watterott/SilentStepStick/hardware/SilentStepStick-TMC2208_v13.jpg

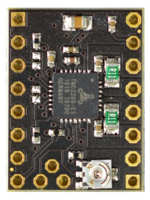
hardware/SilentStepStick-TMC2208_v13.jpg
