watterott/SilentStepStick/hardware/SilentStepStick-TMC2209_v20.jpg

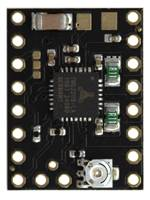
hardware/SilentStepStick-TMC2209_v20.jpg
