watterott/SilentStepStick/hardware/SilentStepStick-TMC5160_v14.pdf

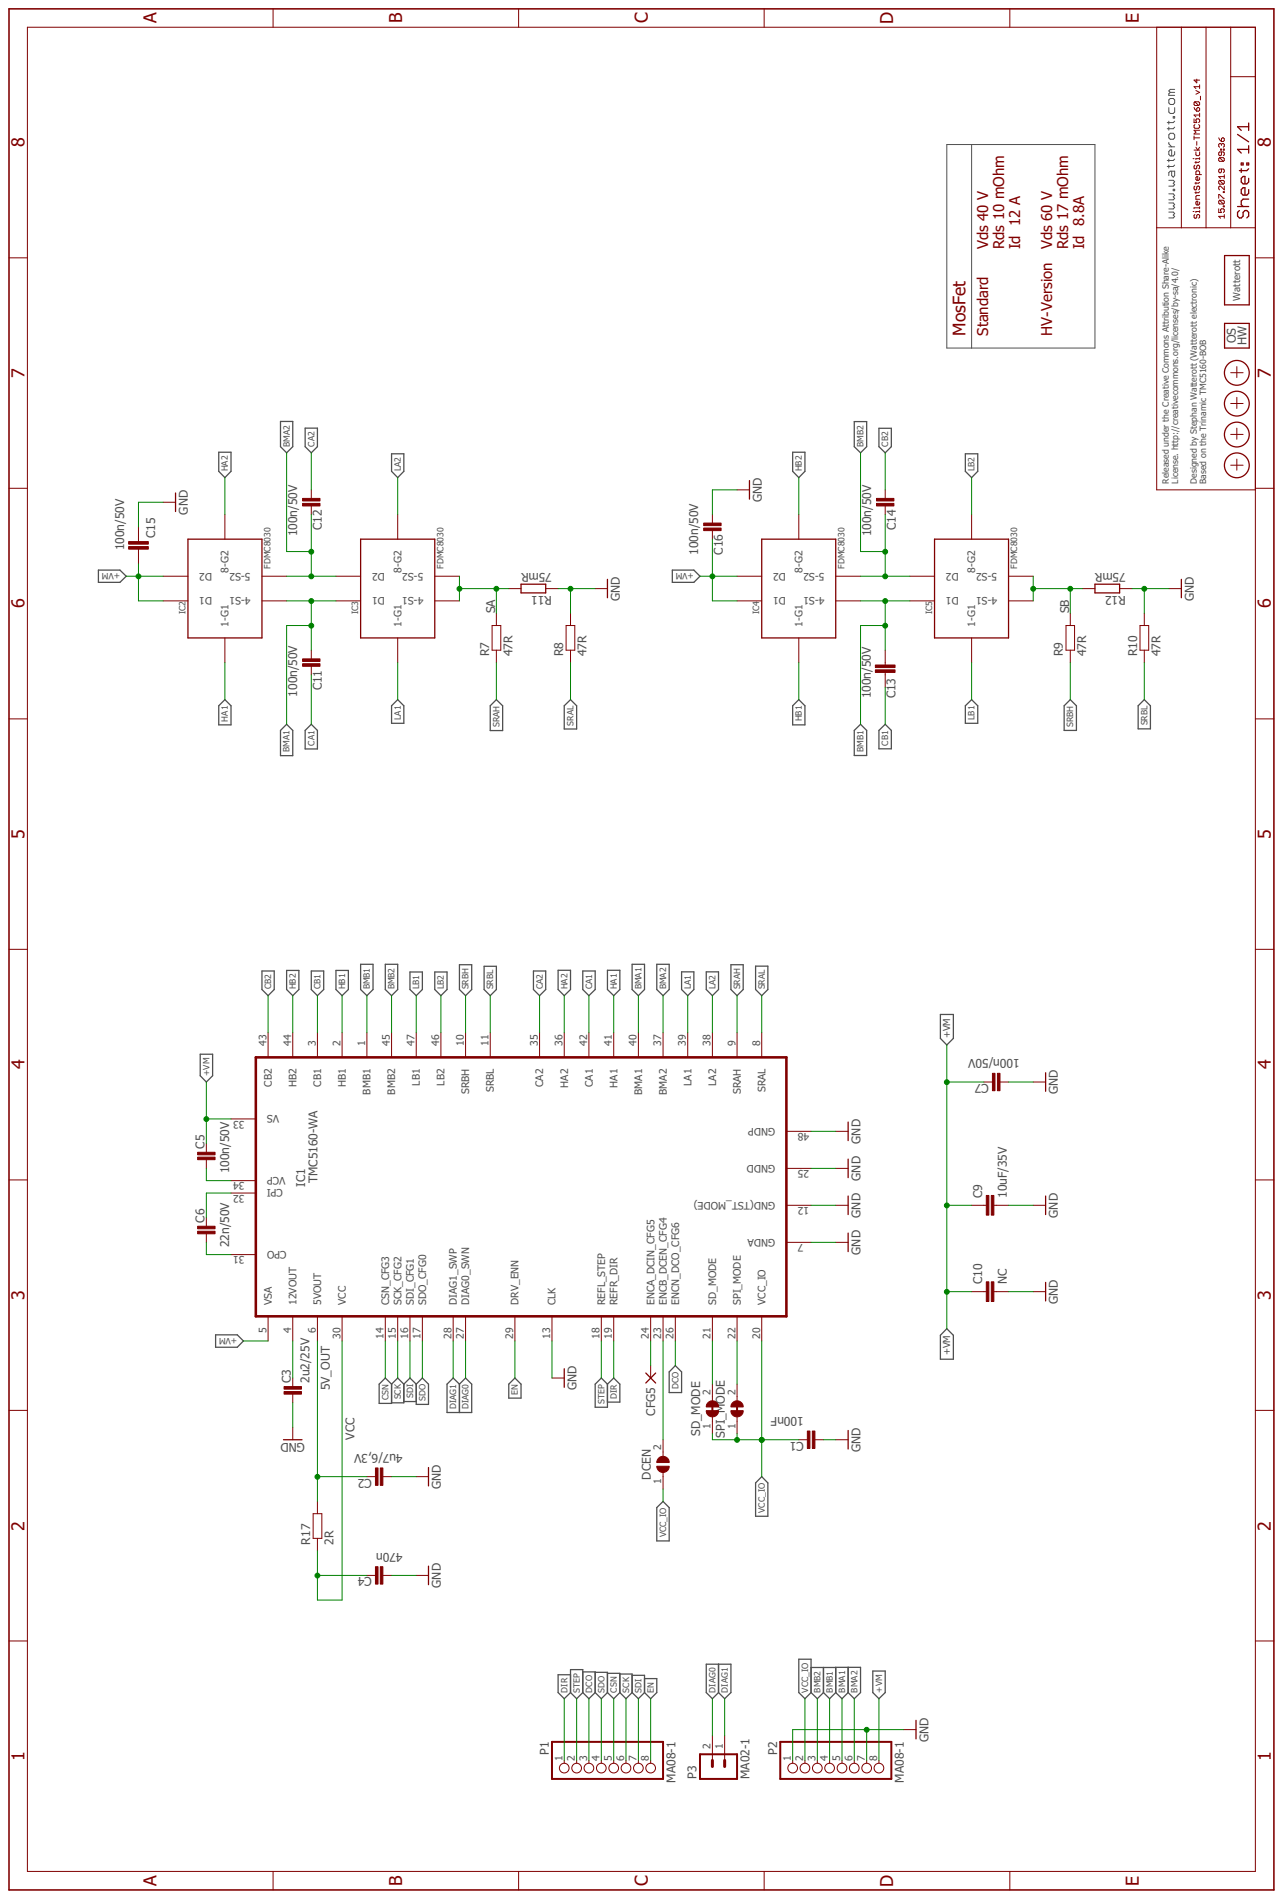
[picture p28: page 1]

MosFet Standard HV-Version

Released under the Creative Commons Attribution Share-Alike

License. http://creativecommons.org/licenses/by-sa/4.0/ Designed by Stephan Watterott (Watterott electronic) Based on the Trinamic TMC5160-BOB

10uF/35V NC GND GND GND

GND GND

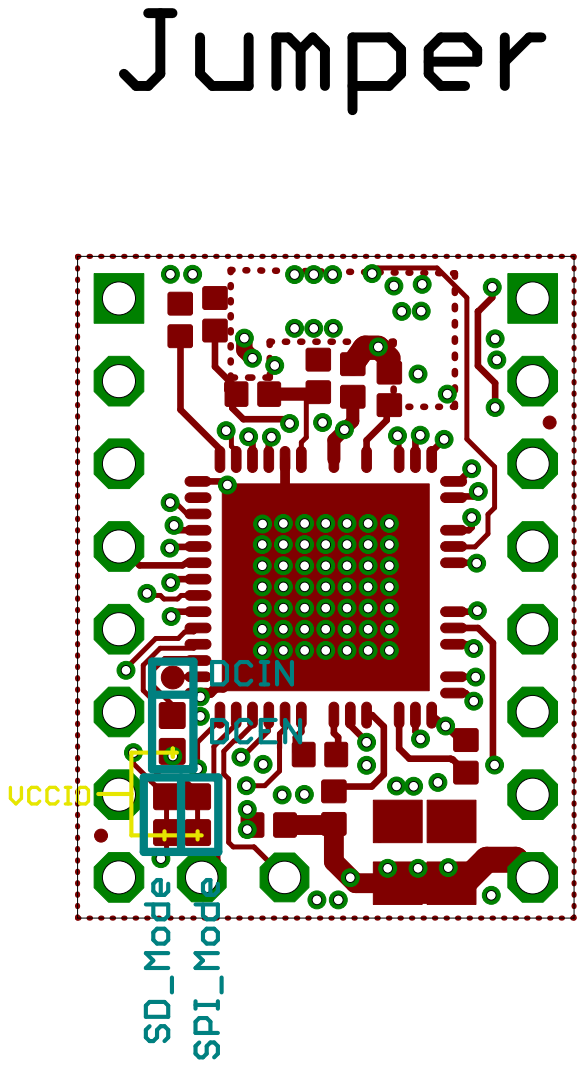
[picture p29: page 2]

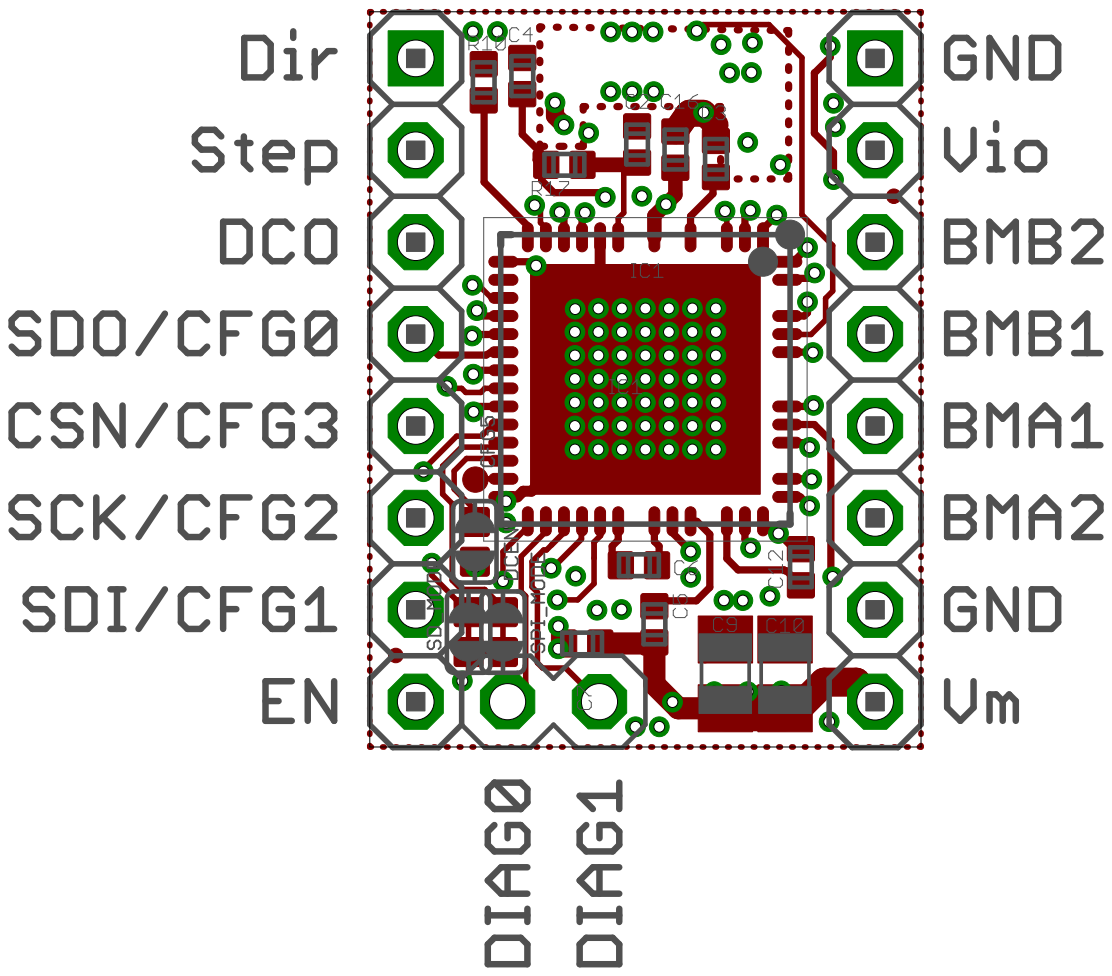
[picture p30: page 3]

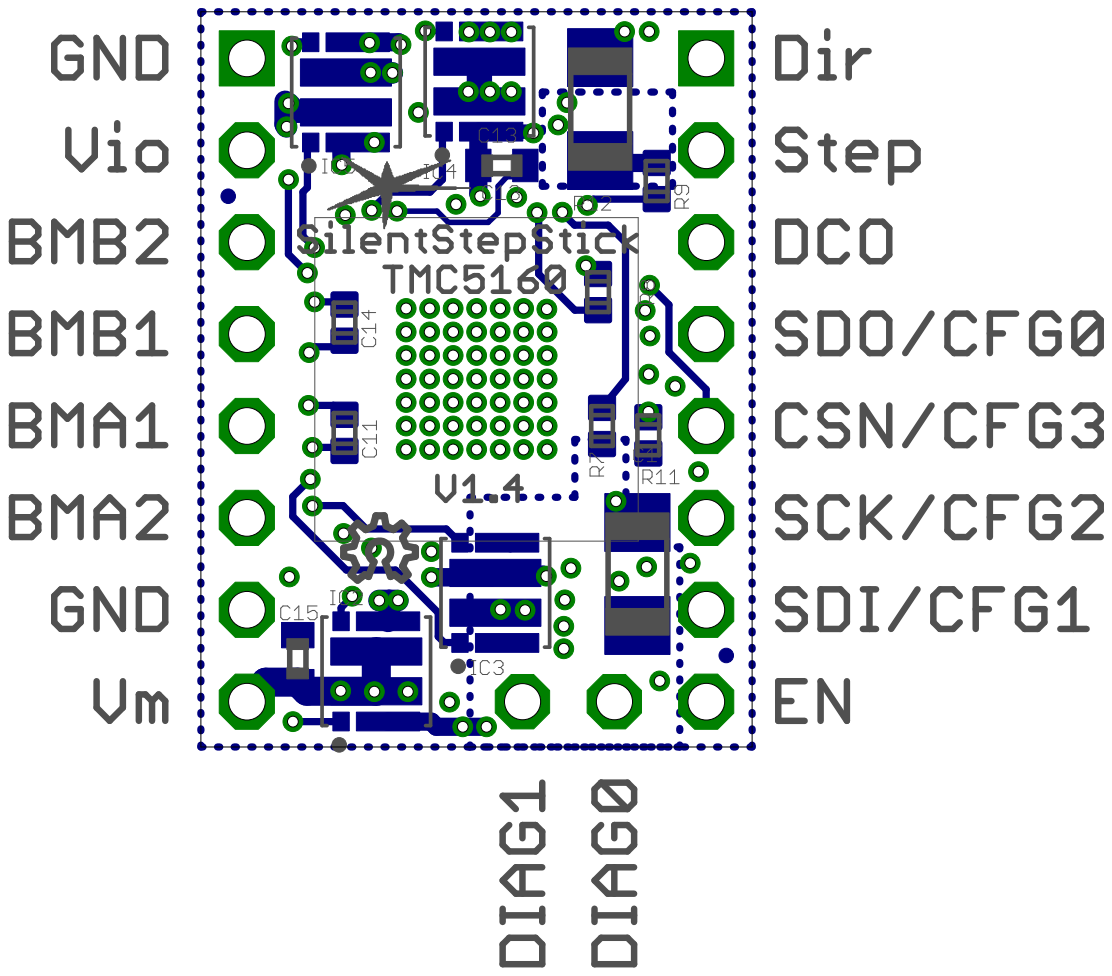
[picture p31: page 4]
