watterott/SilentStepStick/hardware/SilentStepStick-TMC5160_v13.pdf

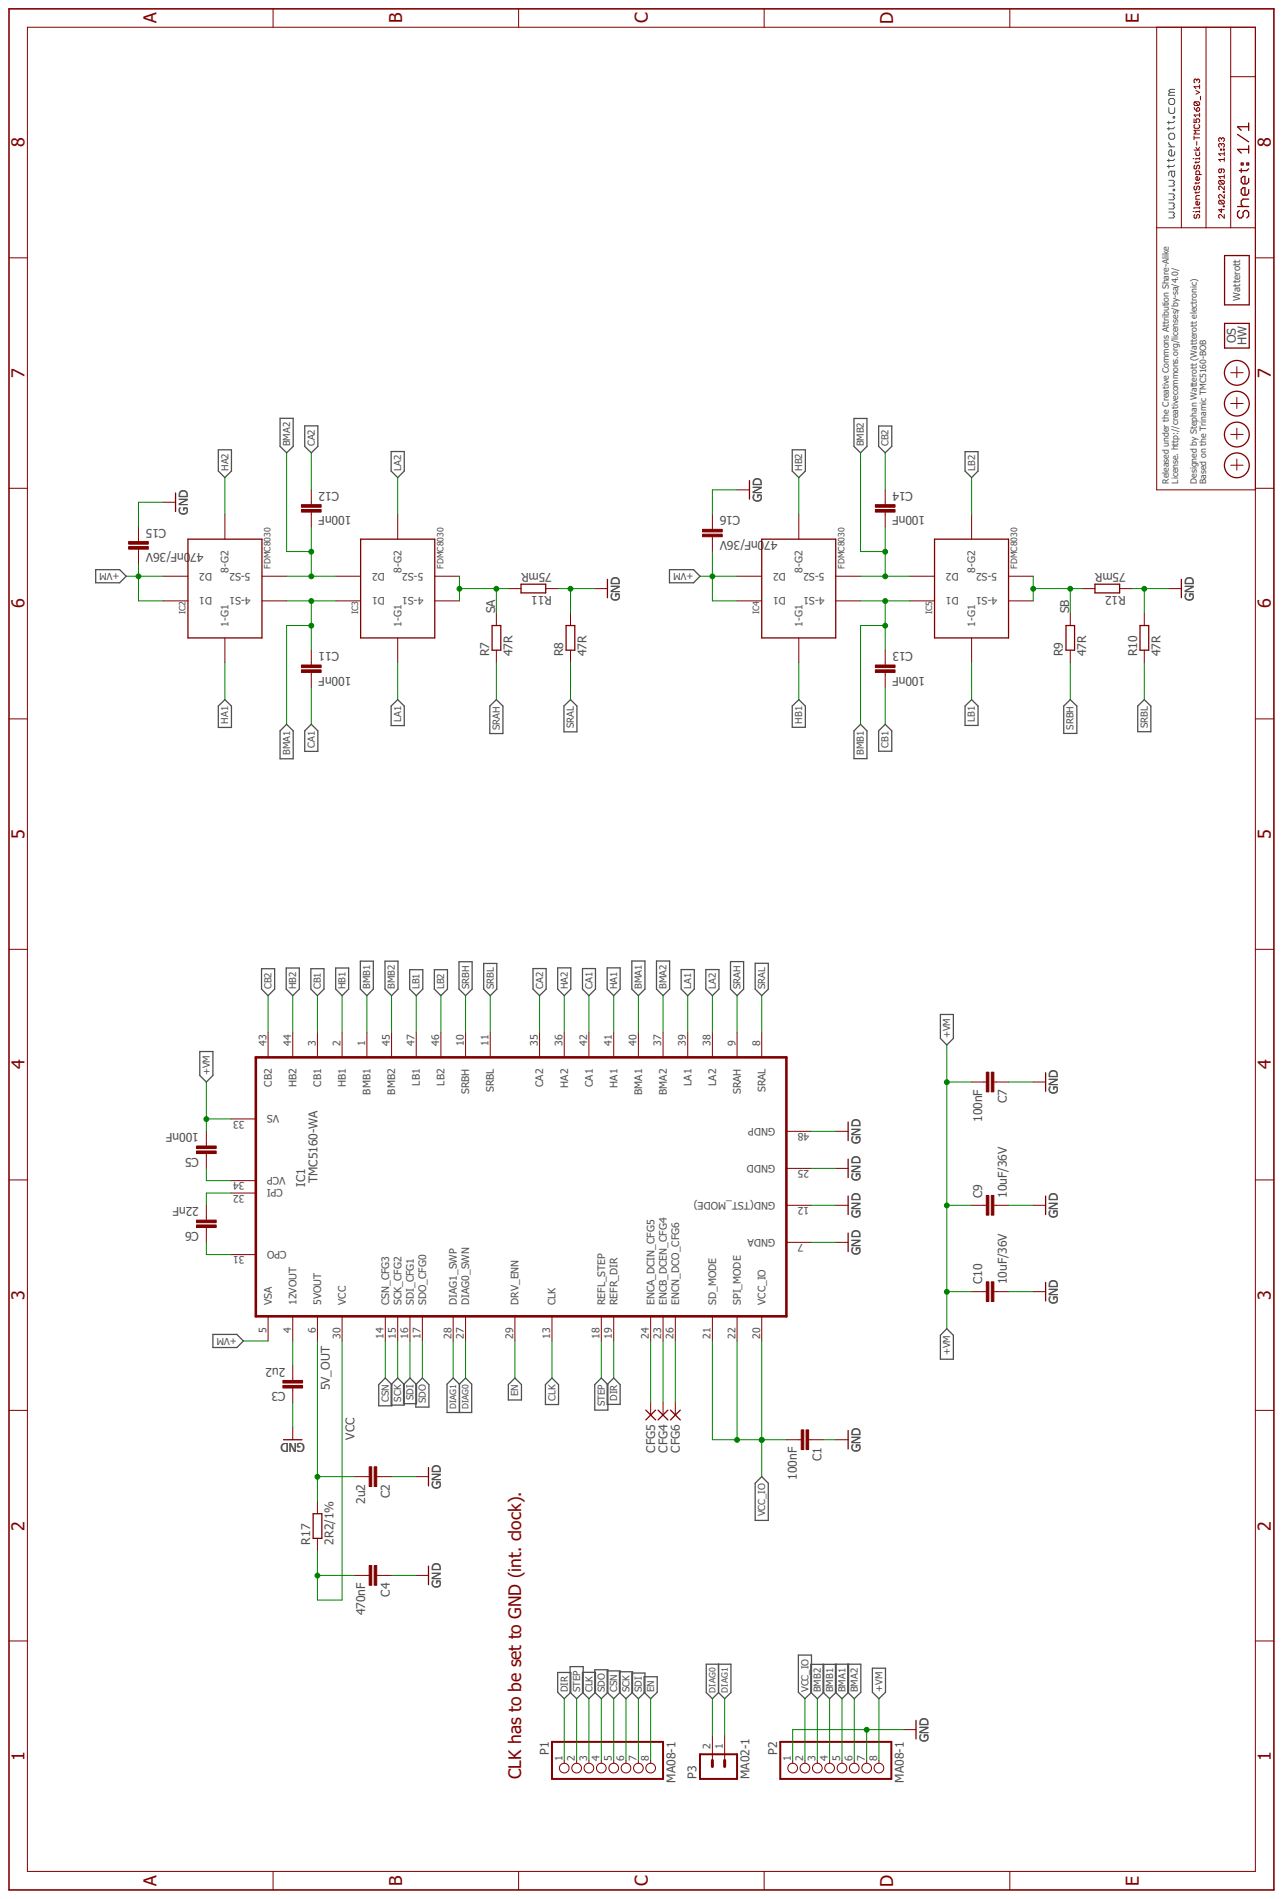
[picture p32: page 1]

Released under the Creative Commons Attribution Share-Alike

License. http://creativecommons.org/licenses/by-sa/4.0/ Designed by Stephan Watterott (Watterott electronic) Based on the Trinamic TMC5160-BOB

GND GND

STEP STEP DIR DIR

CLK has to be set to GND (int. clock).

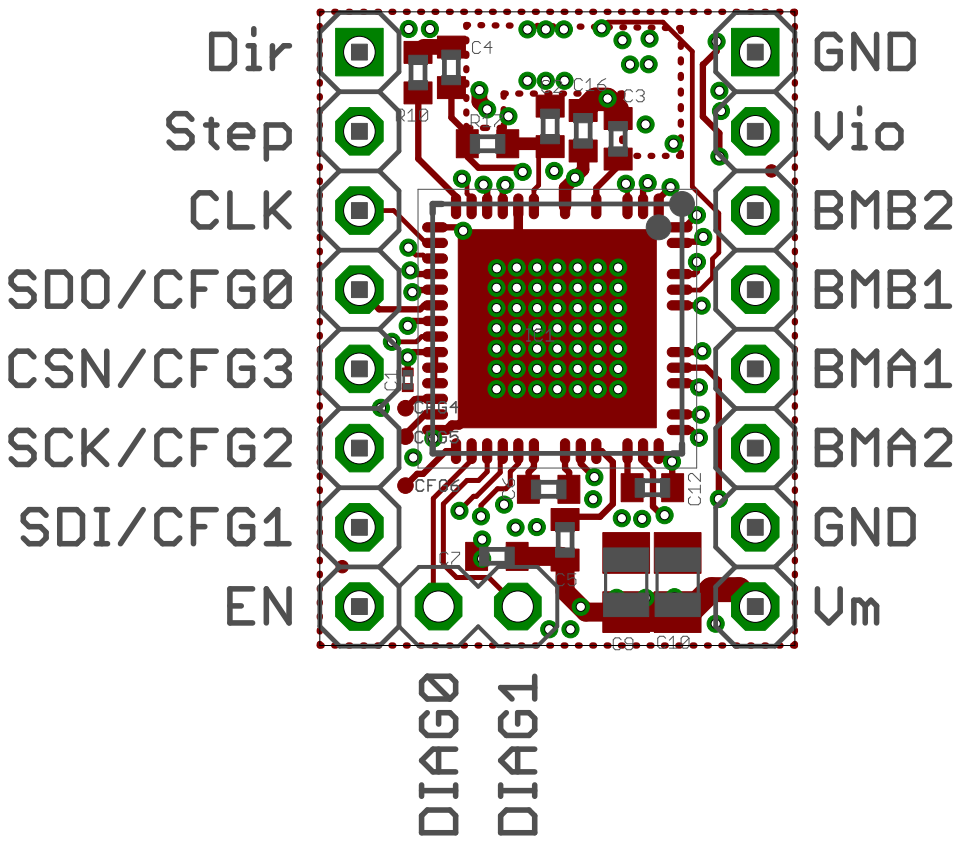
[picture p33: page 2]

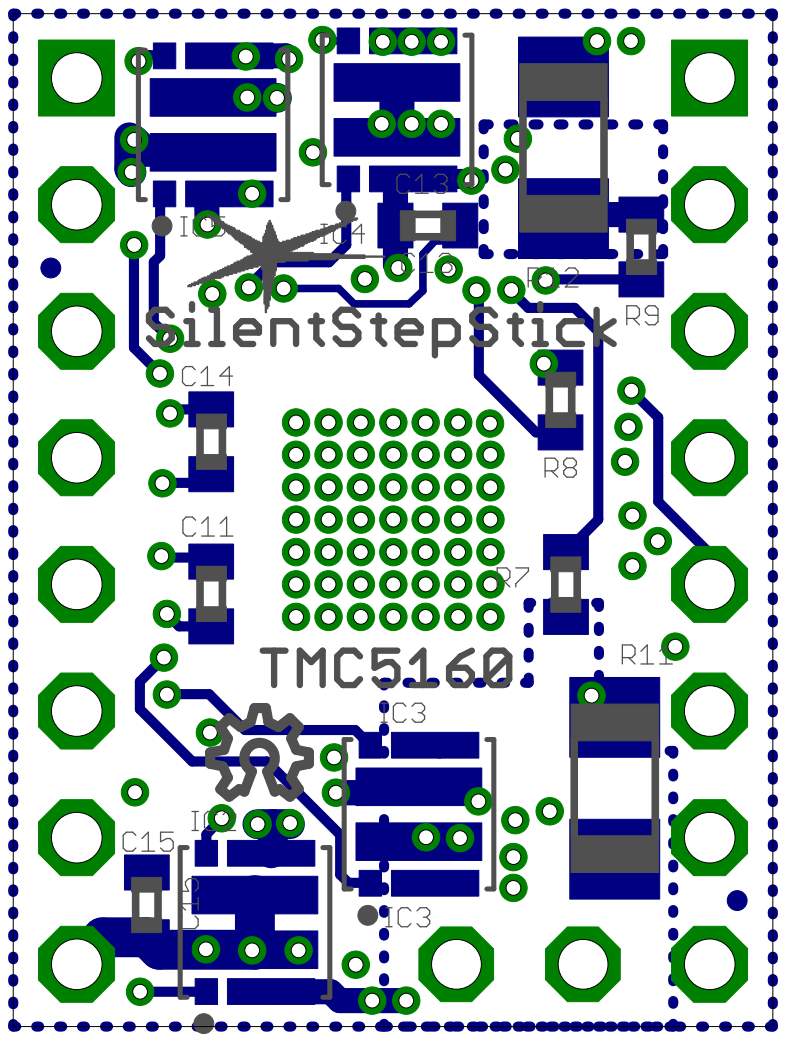
[picture p34: page 3]
