watterott/SilentStepStick/hardware/SilentStepStick-TMC2100_v13_5V.pdf

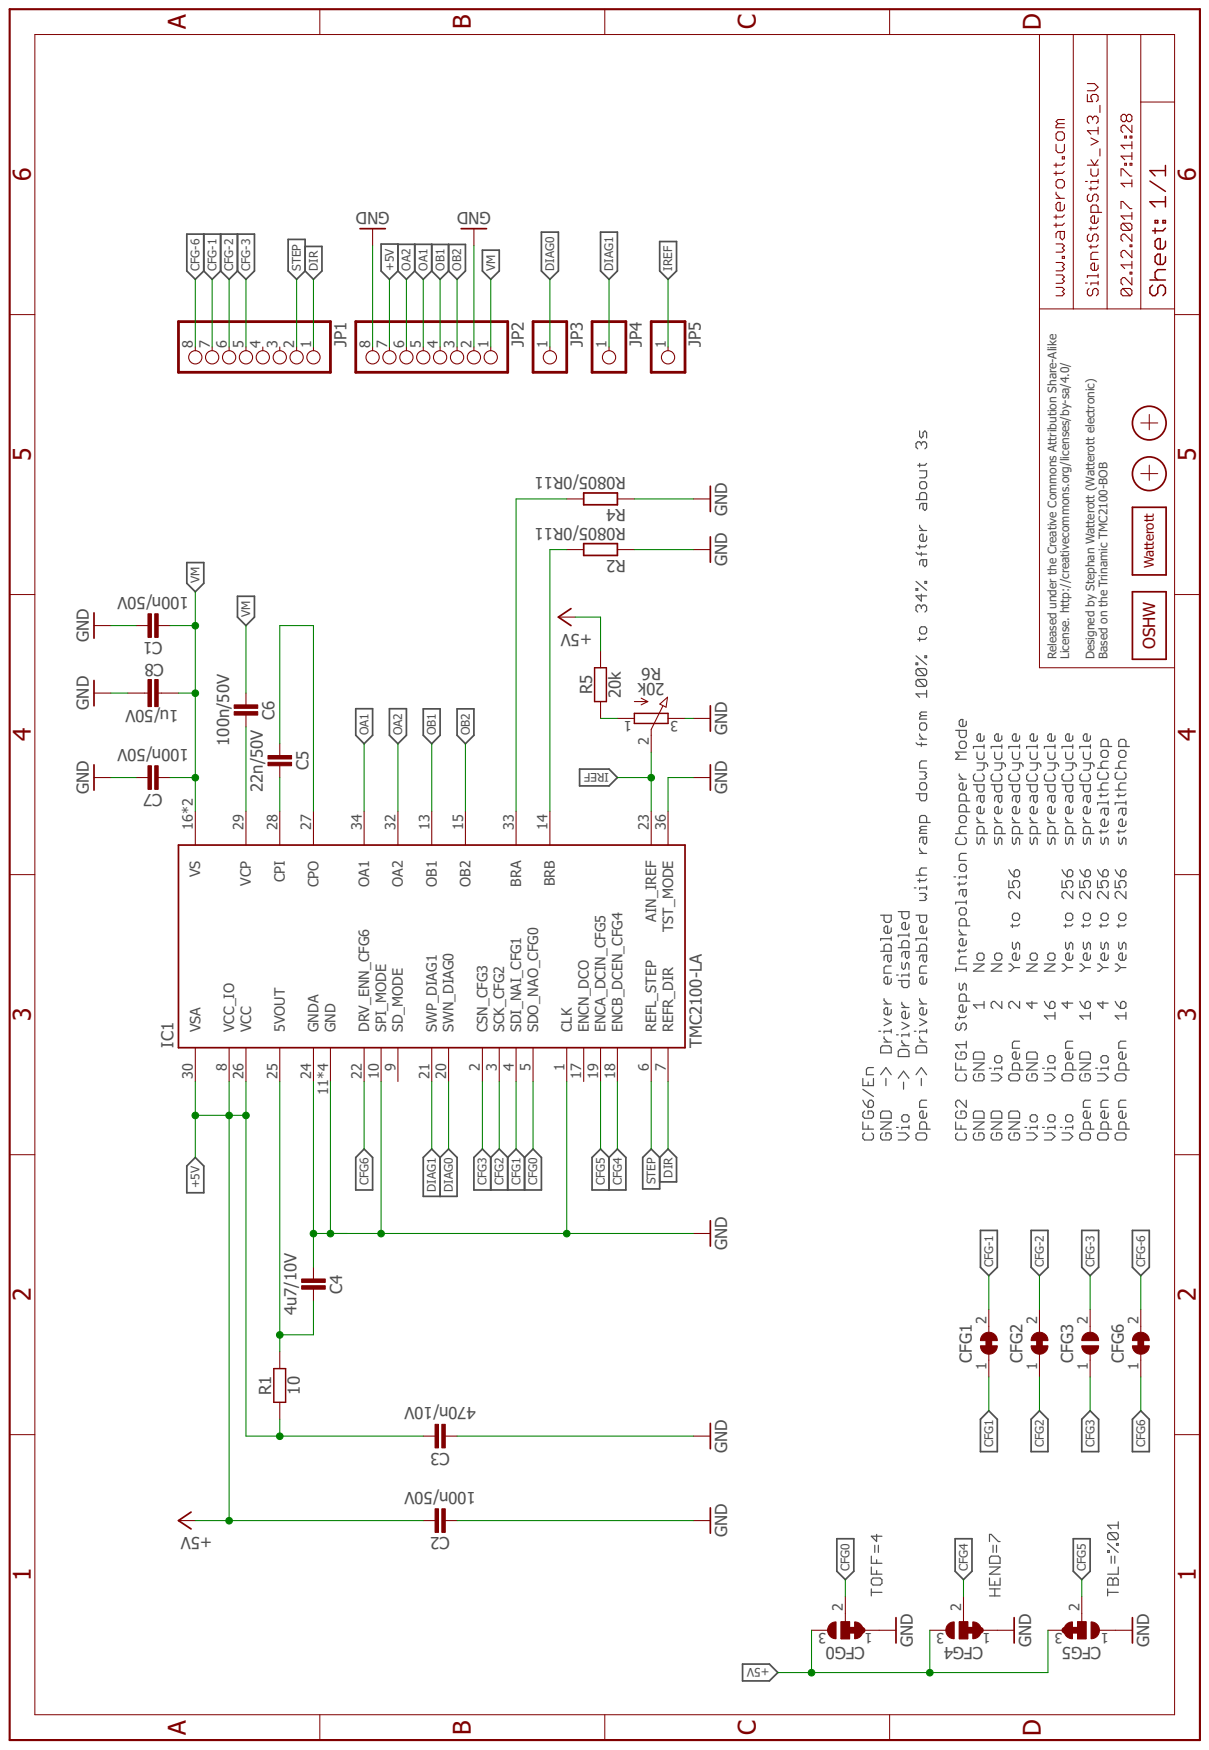
[picture p35: page 1]

Released under the Creative Commons At ribution Share-Alike

License. http://creativecommons.org/licenses/by-sa/4.0/ Designed by Stephan Watterott (Watterott electronic) Based on the Trinamic TMC2100-BOB

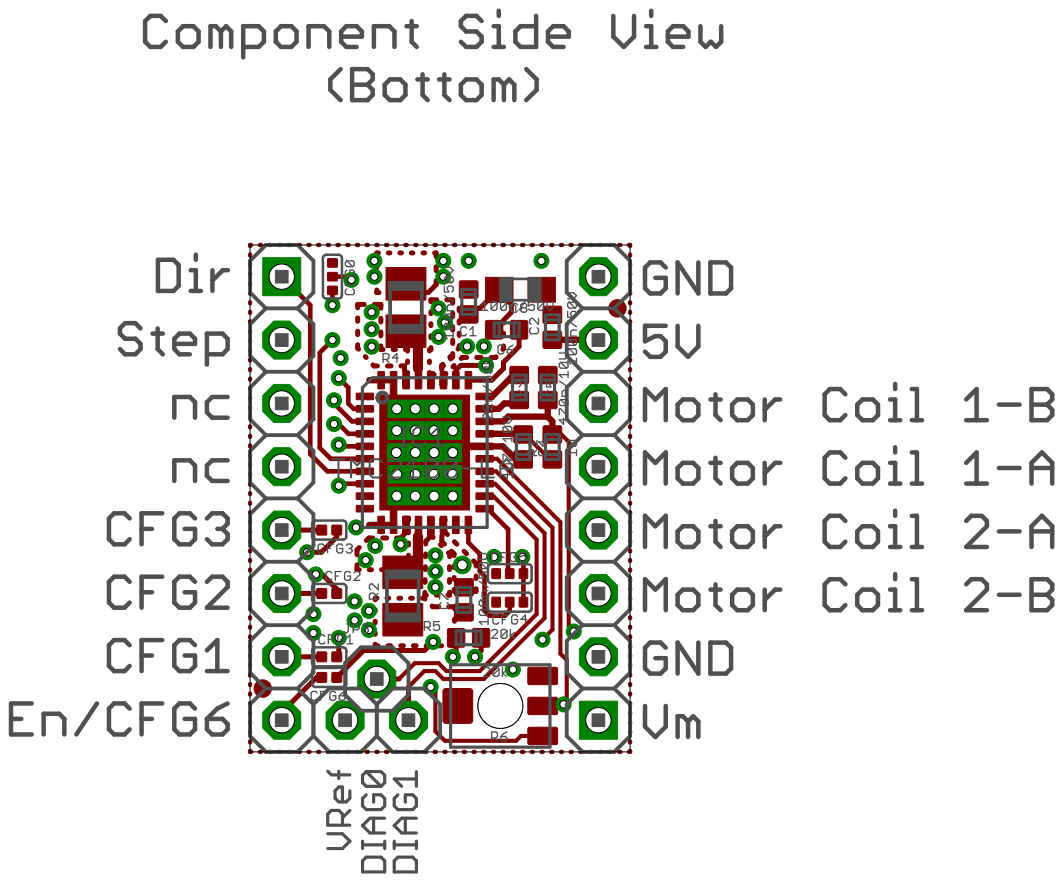
[picture p36: page 2]

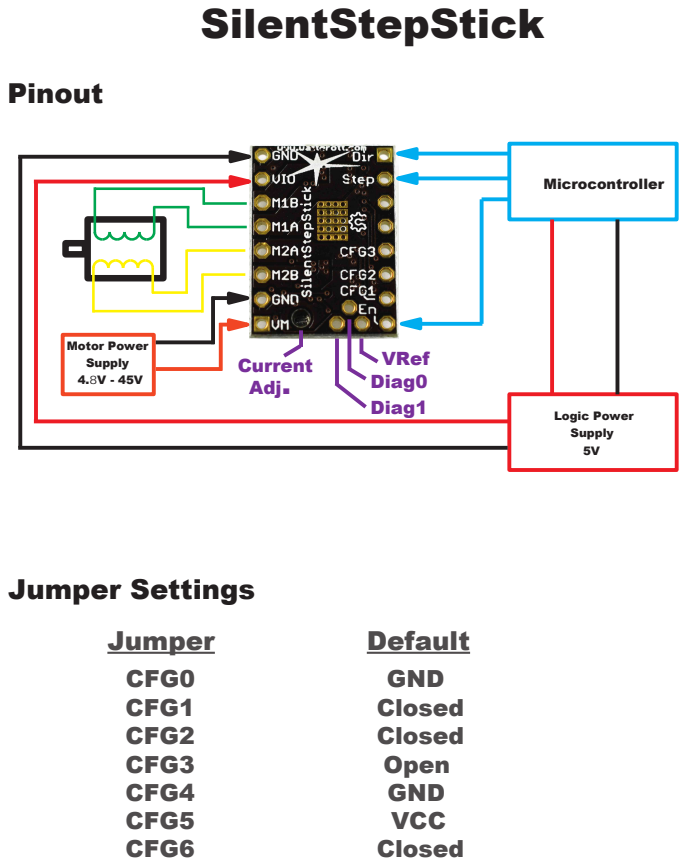
[picture p37: page 3]

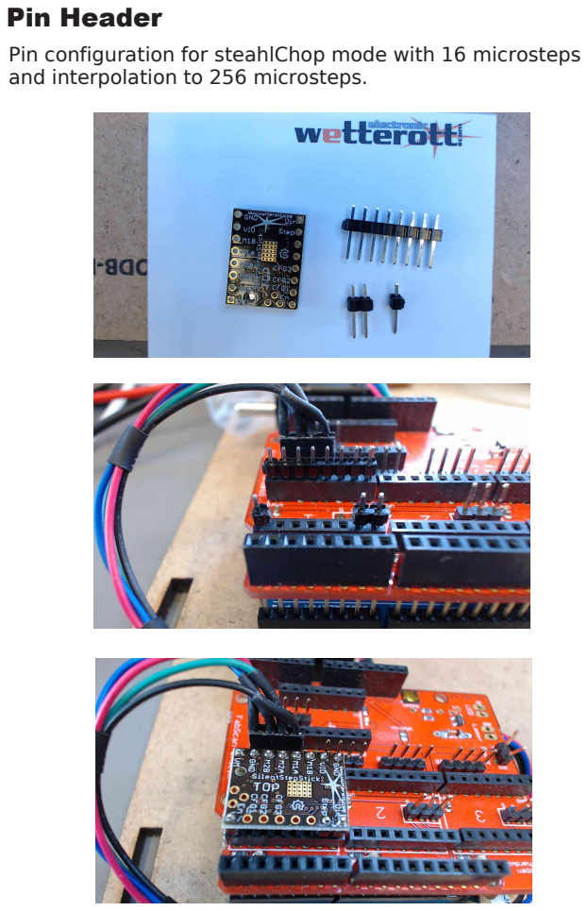
[picture p38: page 4]

Pin configuration for steahlChop mode with 16 microsteps
and interpolation to 256 microsteps.
