watterott/SilentStepStick/hardware/SilentStepStick-TMC2100_v13.pdf

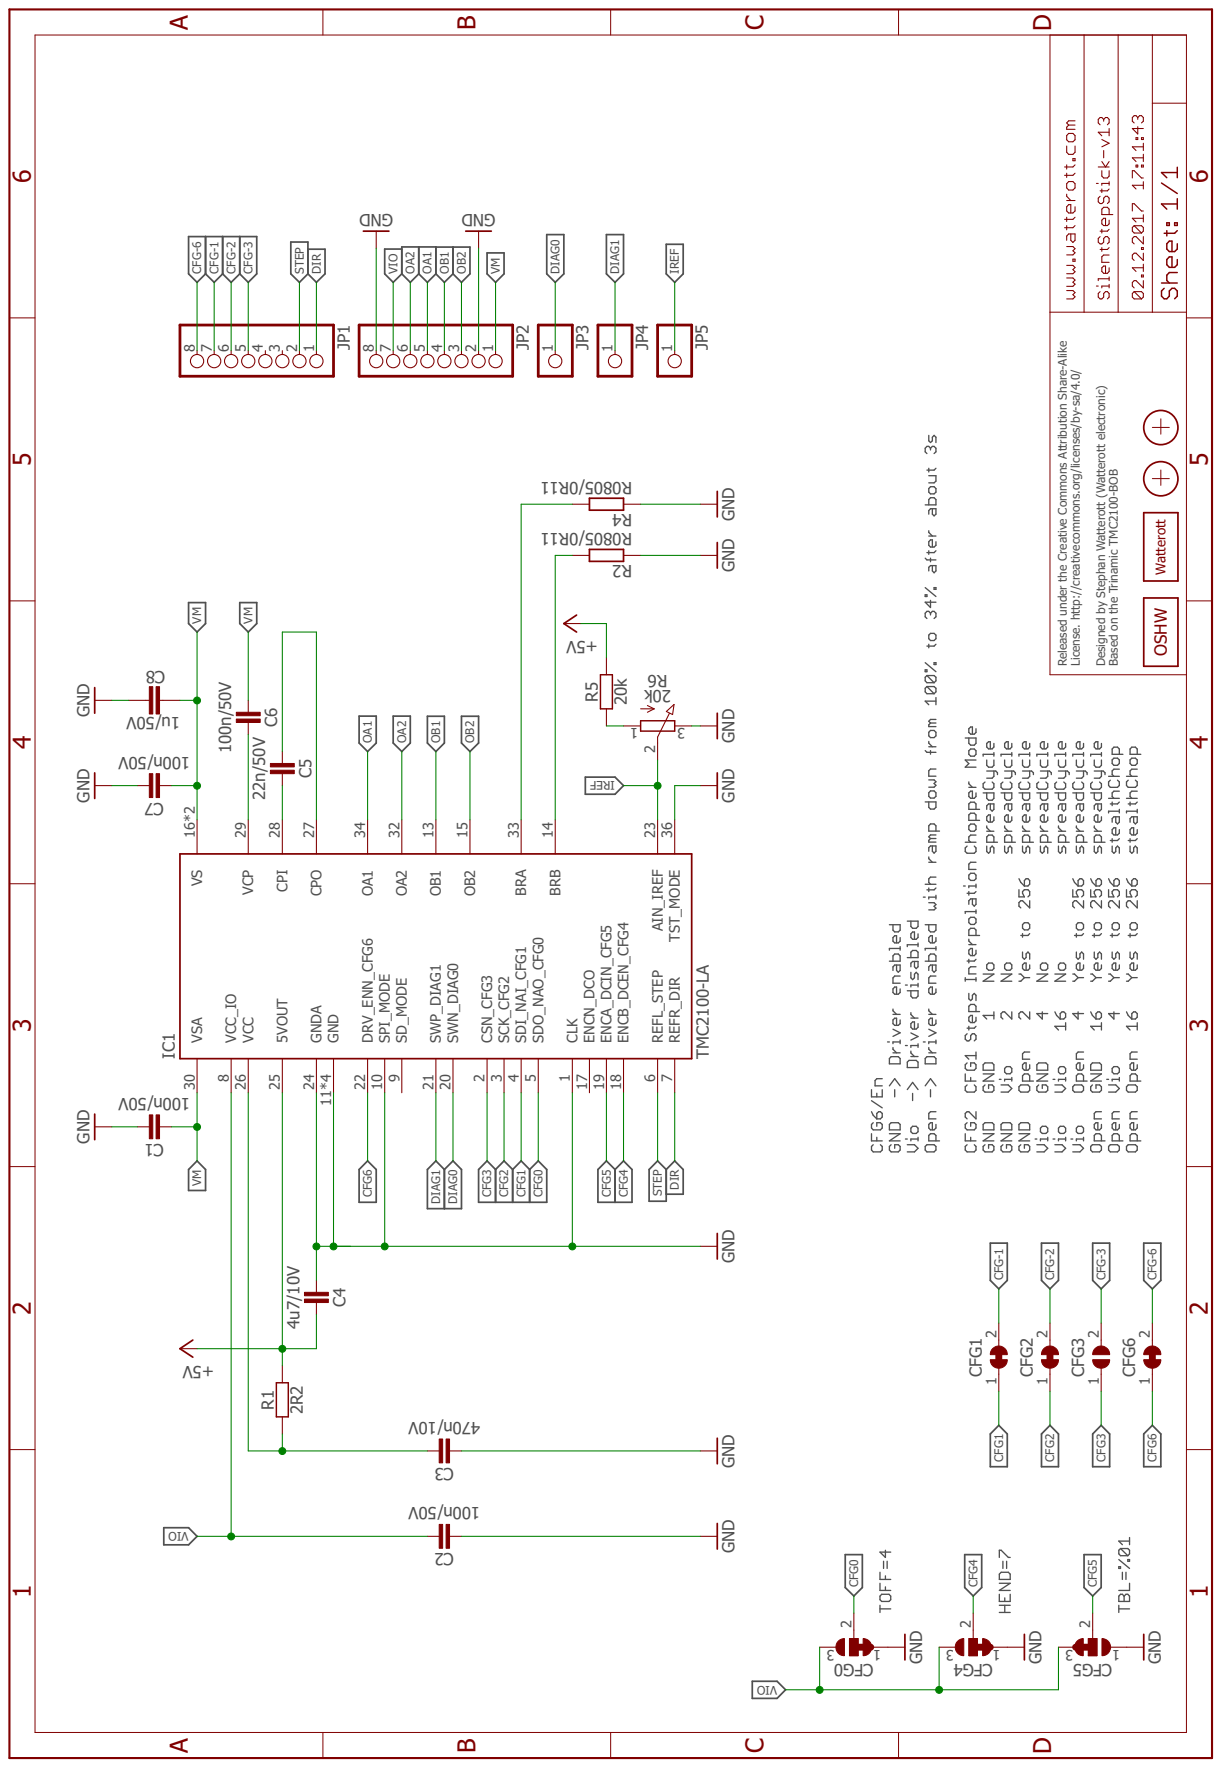
[picture p39: page 1]

Released under the Creative Commons At ribution Share-Alike

License. http://creativecommons.org/licenses/by-sa/4.0/ Designed by Stephan Watterott (Watterott electronic) Based on the Trinamic TMC2100-BOB

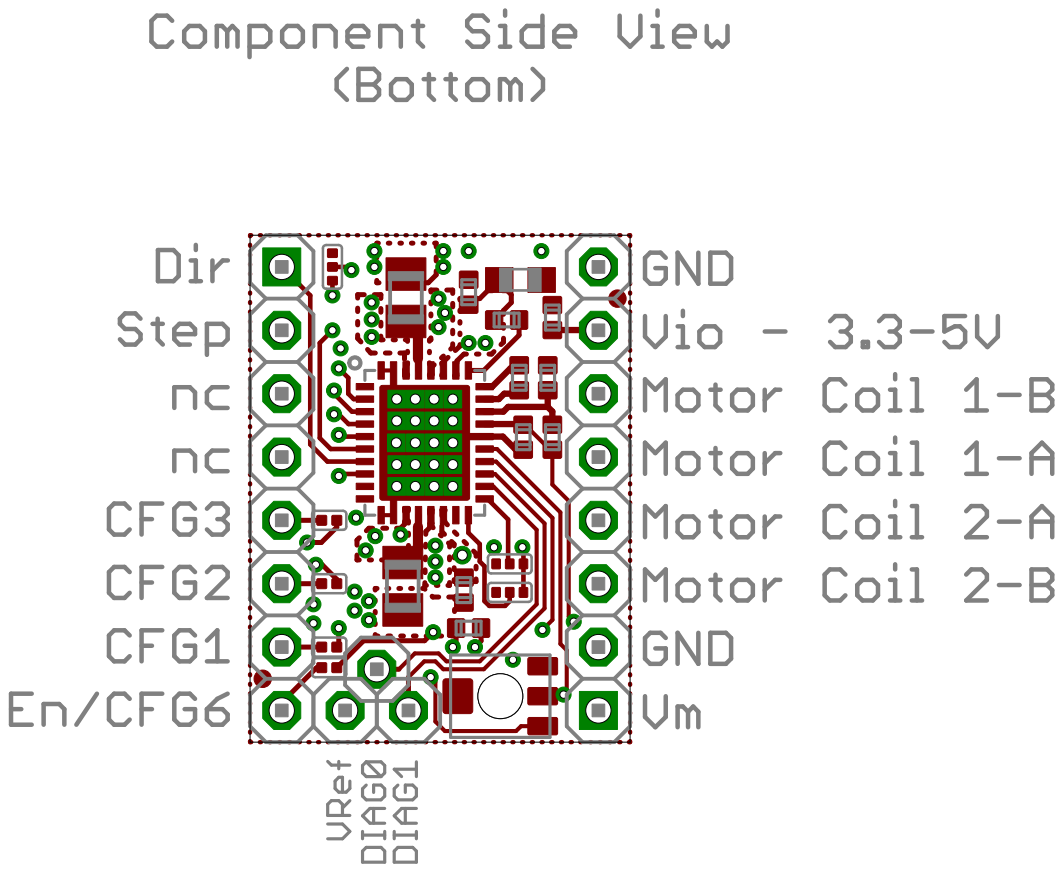
[picture p40: page 2]

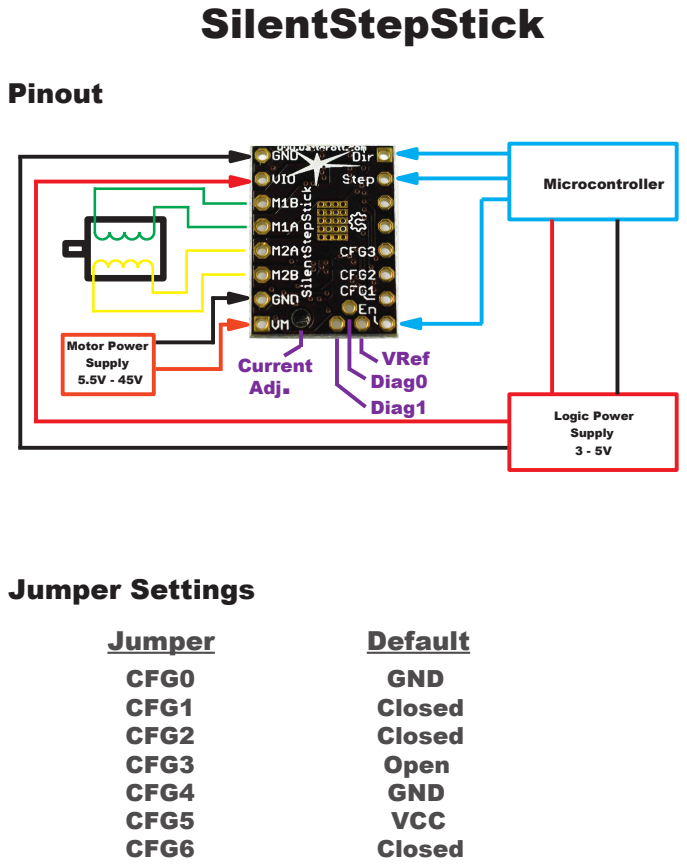
[picture p41: page 3]


Pin configuration for steahlChop mode with 16 microsteps
and interpolation to 256 microsteps.
