watterott/SilentStepStick/hardware/SilentStepStick-TMC2100_v11.pdf

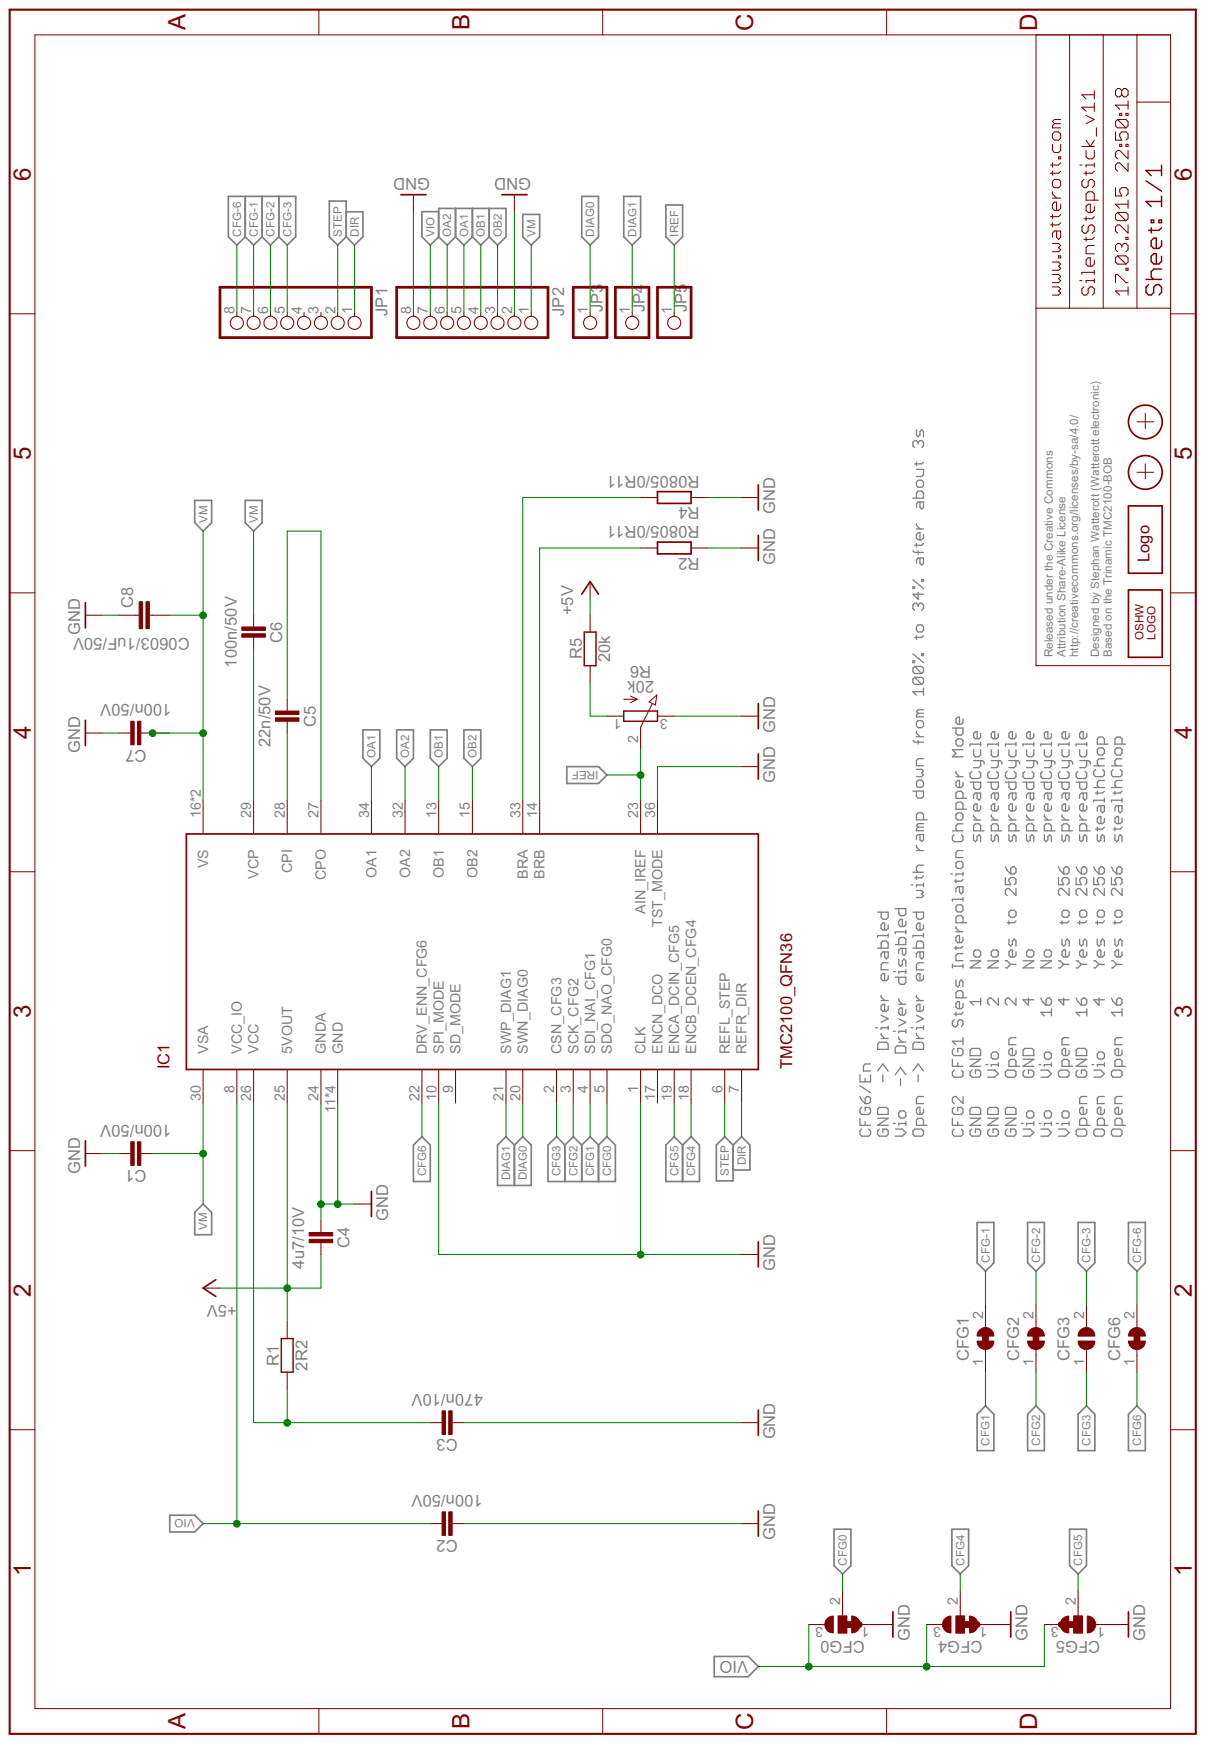
[picture p42: page 1]

Designed by Stephan Watterott (Watterott electronic)

http://creativecommons.org/licenses/by-sa/4.0/

Released under the Creative Commons

Based on the Trinamic TMC2100-BOB

GND GND

Attribution Share-Alike License

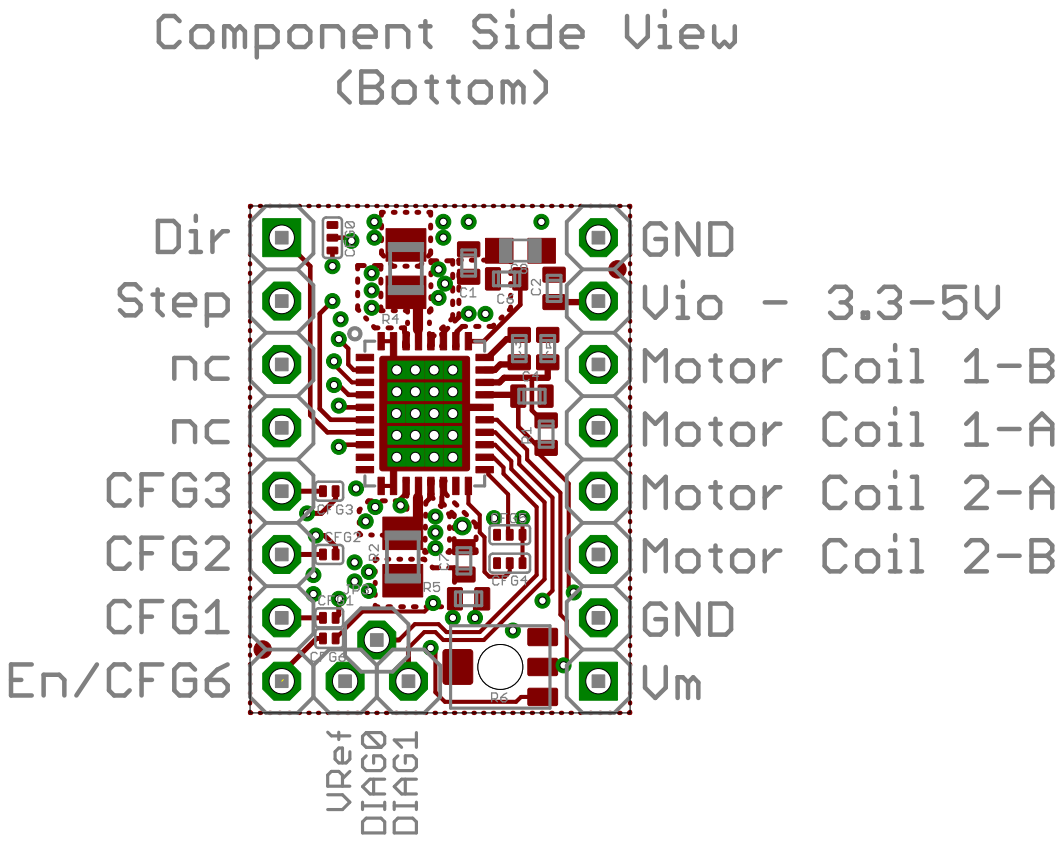
[picture p43: page 2]



Pin configuration for steahlChop mode with 16 microsteps
and interpolation to 256 microsteps.
