watterott/SilentStepStick/hardware/SilentStepStick-TMC2100_v12_5V.pdf

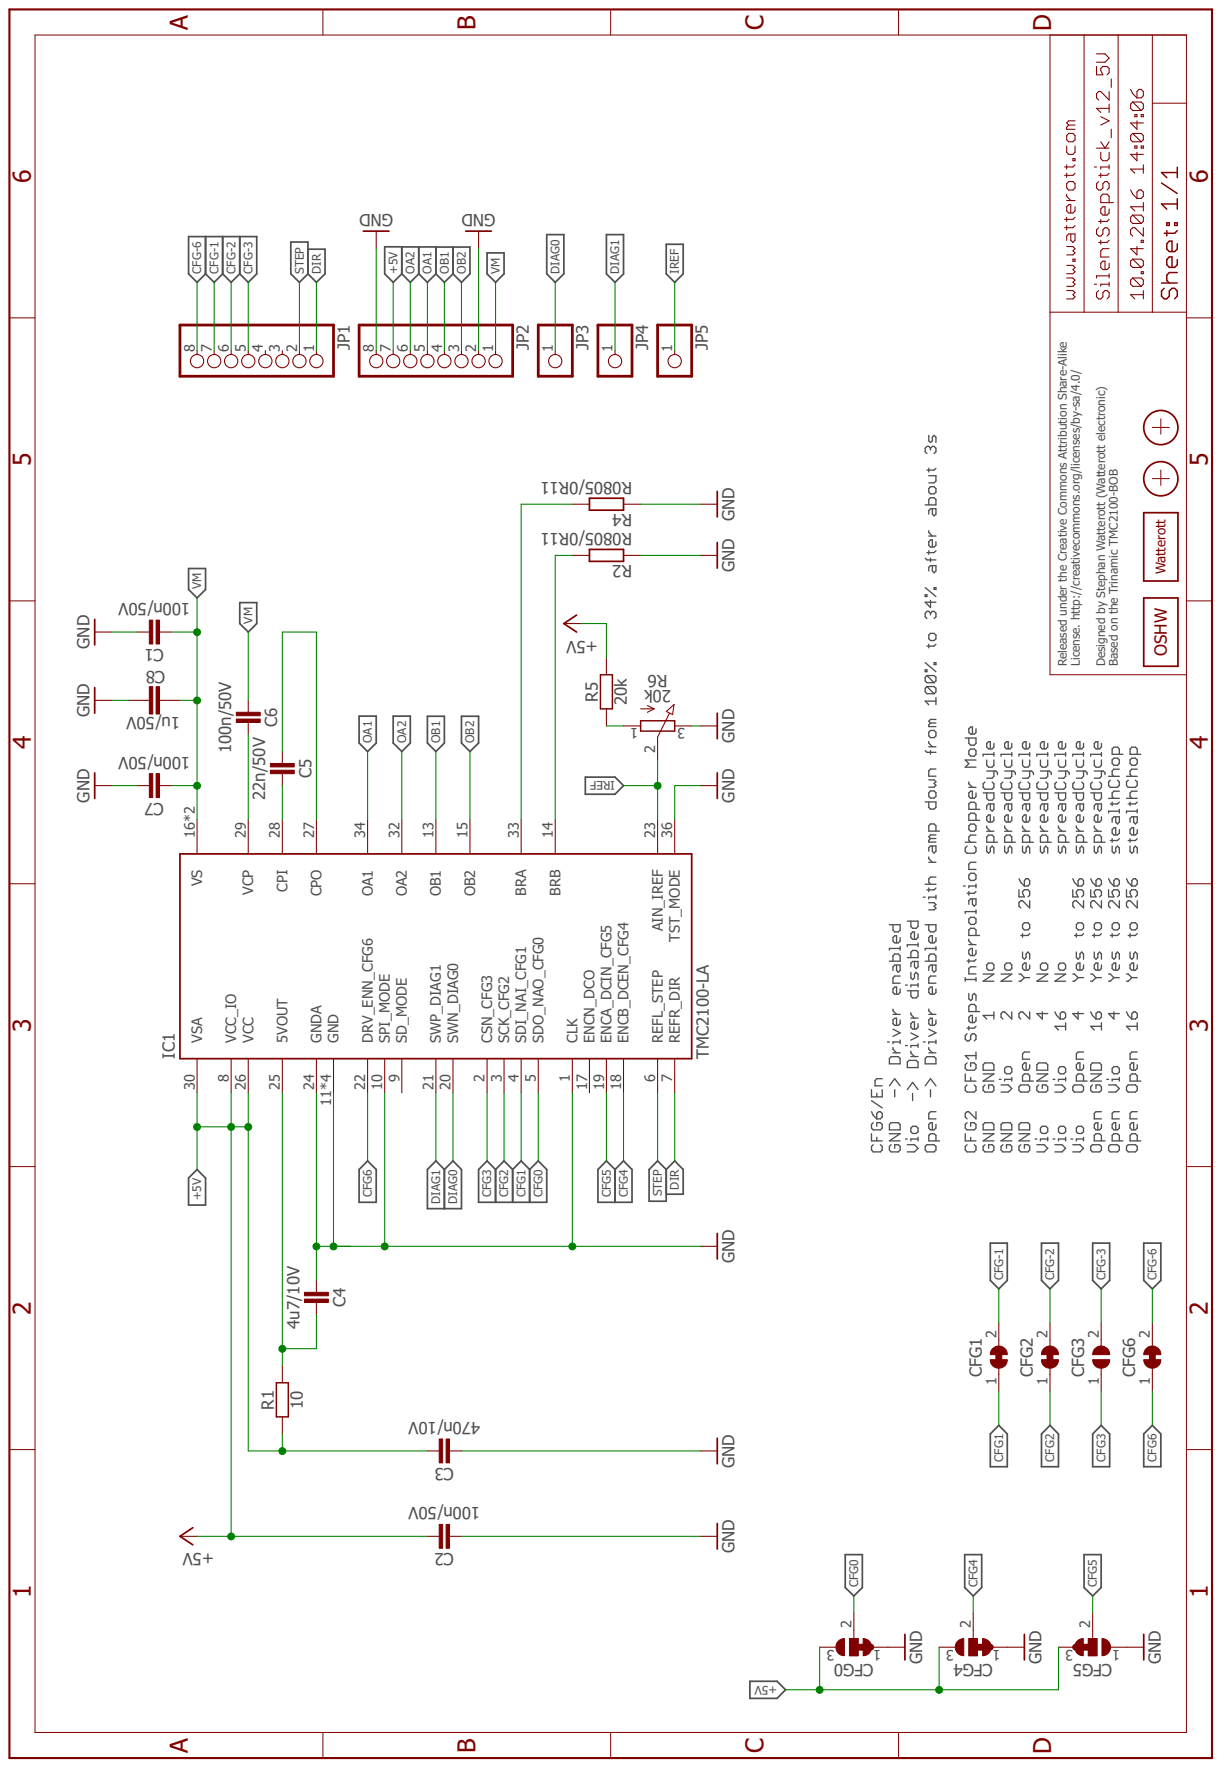
[picture p44: page 1]

Released under the Creative Commons At ribution Share-Alike

License. ht p://creativecommons.org/licenses/by-sa/4.0/ Designed by Stephan Wat erot (Wat erot electronic) Based on the Trinamic TMC2100-BOB




Pin configuration for steahlChop mode with 16 microsteps
and interpolation to 256 microsteps.
