watterott/SilentStepStick/hardware/StepStick-Protector_v10.pdf

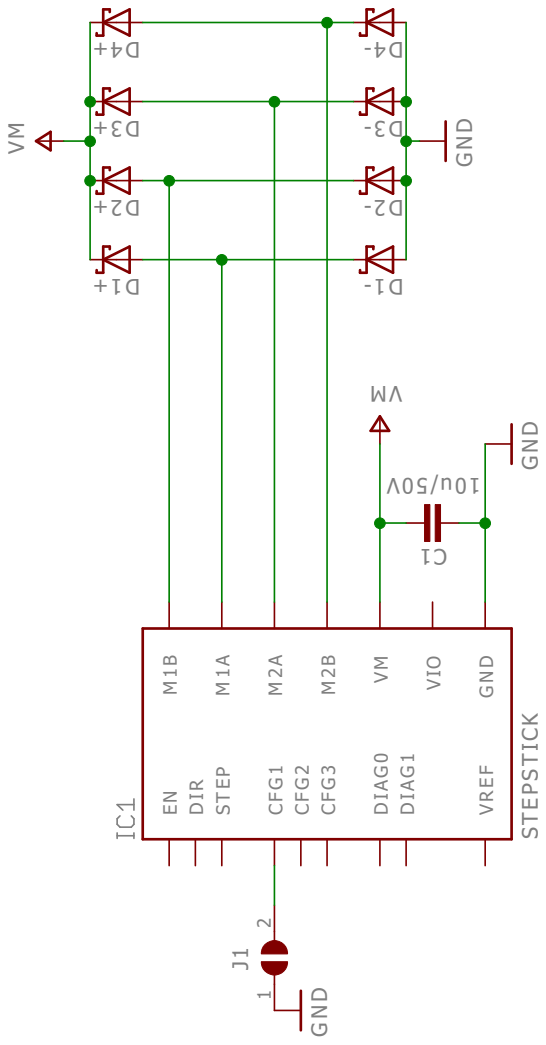
[picture p45: page 1]

GND VM MV GND V05/ u01 GND Released under the Creative Commons Attribution Share-Alike License http://creativecommons.org/licenses/by-sa/4.0/ Designed by Andreas Watterott (Watterott electronic) STEPSTICK DIR STEP CFG1 CFG2 CFG3 DIAG0 EN VM VIO GND M1A DIAG1 M2A M1B M2B VREF +1 D +2 D +3 D +4 D - 1 D - 2 D - 3 D - 4 D 1 C J1 2 1 ABCD 1 2 3 4 5 6 ABCD 1 2 3 4 5 6 OSHW LOGO Logo

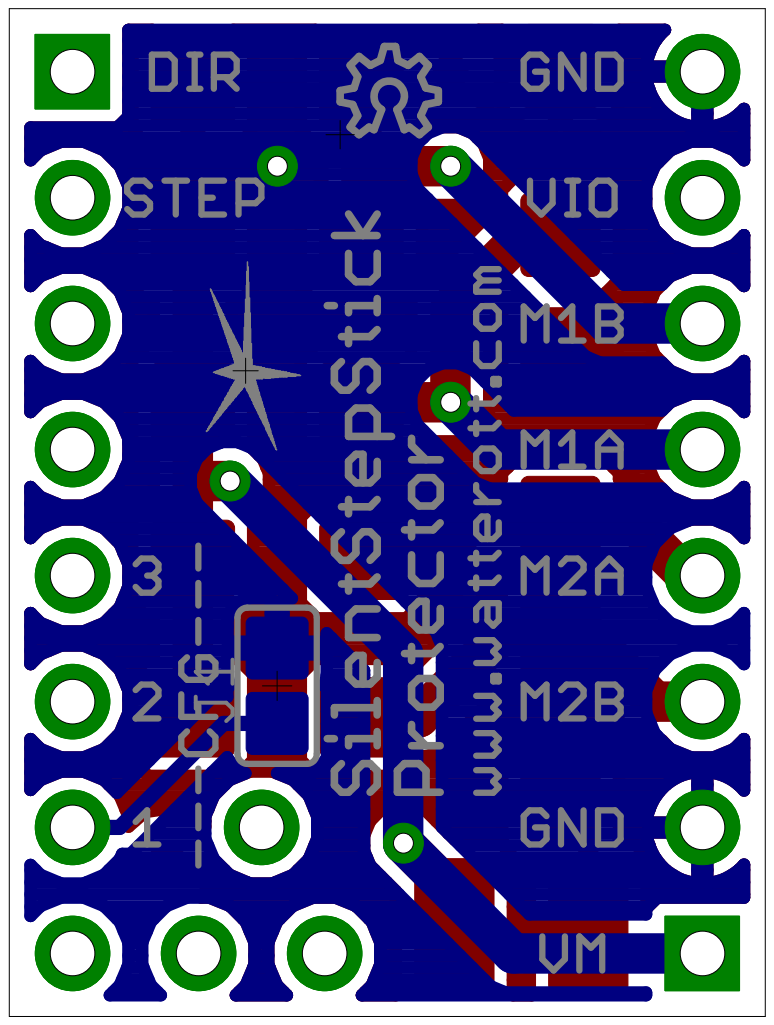
[picture p46: page 2]
