watterott/SilentStepStick/hardware/StepStick-Protector_v11.pdf

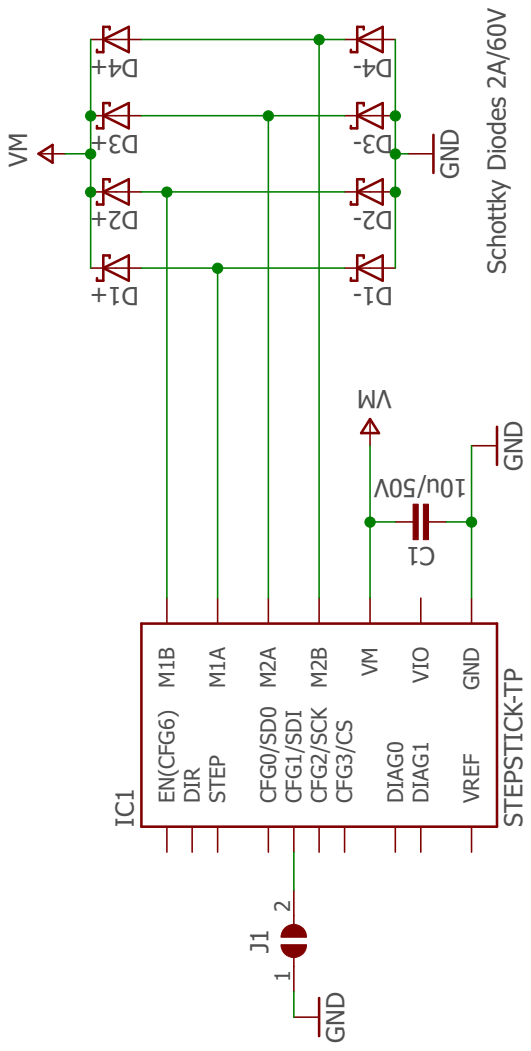
[picture p47: page 1]

Schottky Diodes 2A/60V GNDVM MV GND V05/ u01 GND Released under the Creative Commons At ribution Share-Alike License http://creativecommons.org/licenses/by-sa/4.0/ Designed by Andreas Watterott (Watterott electronic) IC1 STEPSTICK-TP DIR STEP CFG1/SDI CFG2/SCK CFG3/CS DIAG0 EN(CFG6) VMVIO GND M1A DIAG1 M2A M1B M2B VREF CFG0/SD0 +1D +2D +3D +4D - 1D - 2D - 3D - 4D 1C J1 2 1 ABCD 1 2 3 4 5 6 ABCD 1 2 3 4 5 6 OSHW Watterott

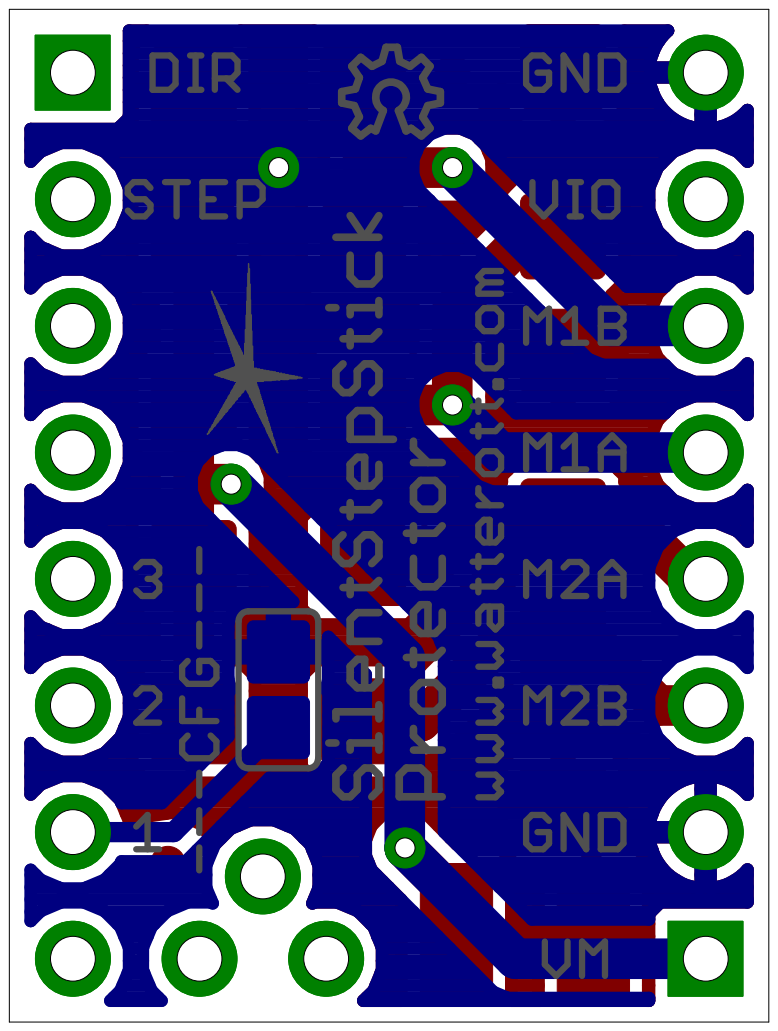
[picture p48: page 2]
