watterott/SilentStepStick/hardware/SilentStepStick-TMC2130_v11.pdf

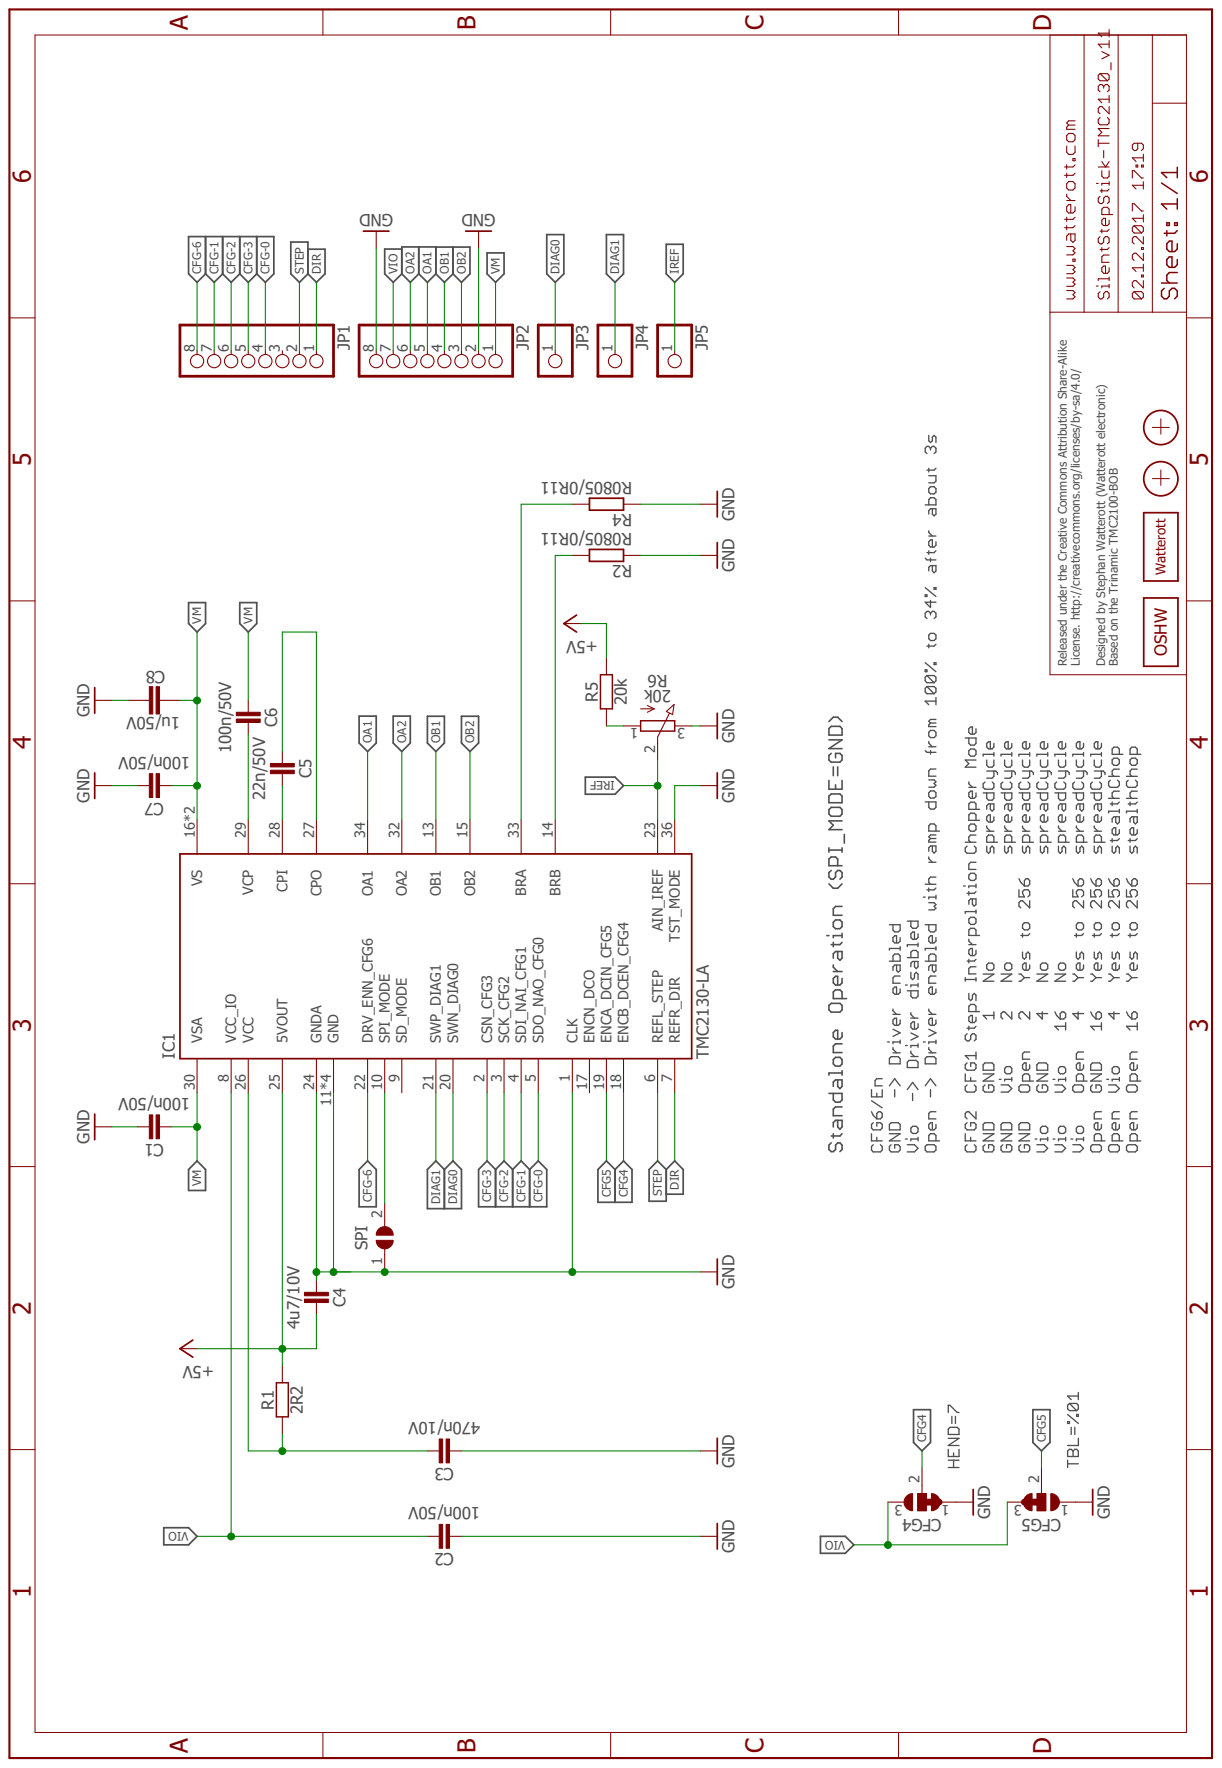
[picture p51: page 1]

Released under the Creative Commons Attribution Share-Alike

License. http://creativecommons.org/licenses/by-sa/4.0/ Designed by Stephan Watterott (Watterott electronic) Based on the Trinamic TMC2100-BOB

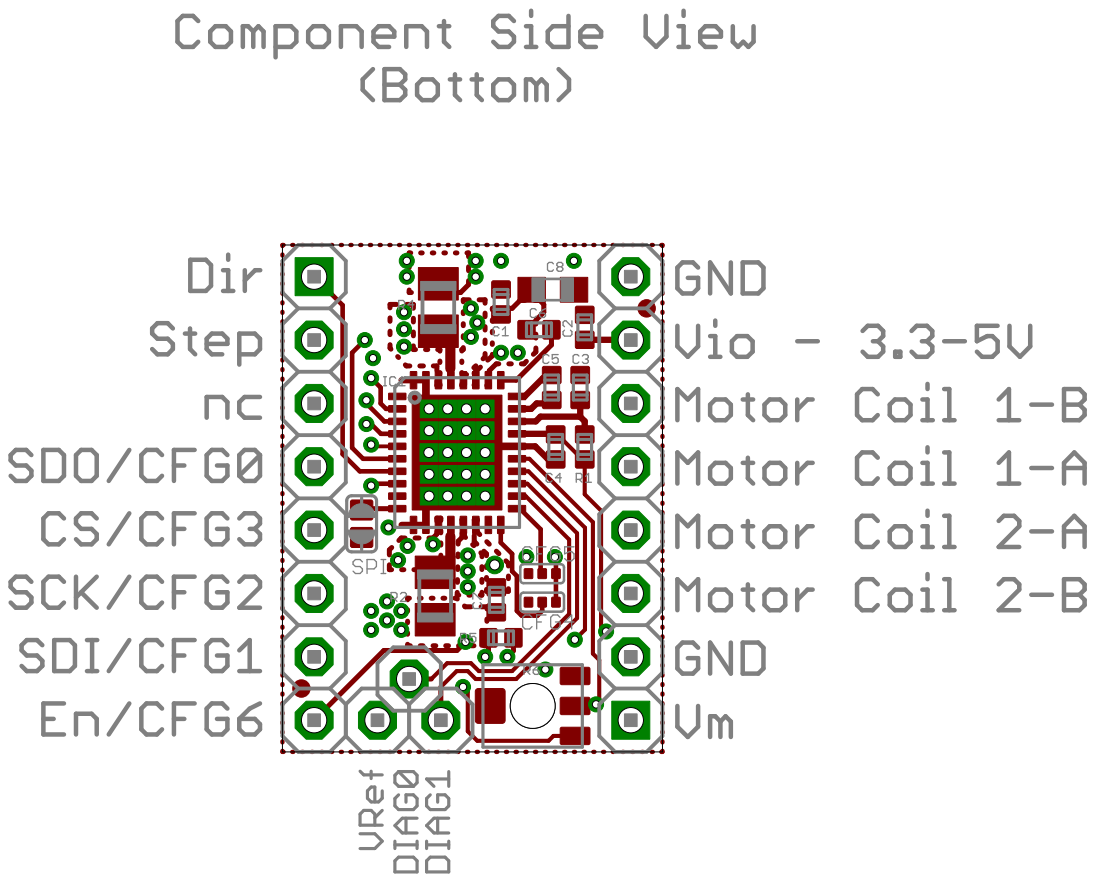
[picture p52: page 2]
