watterott/SilentStepStick/hardware/SilentStepStick-TMC2100_v10.pdf

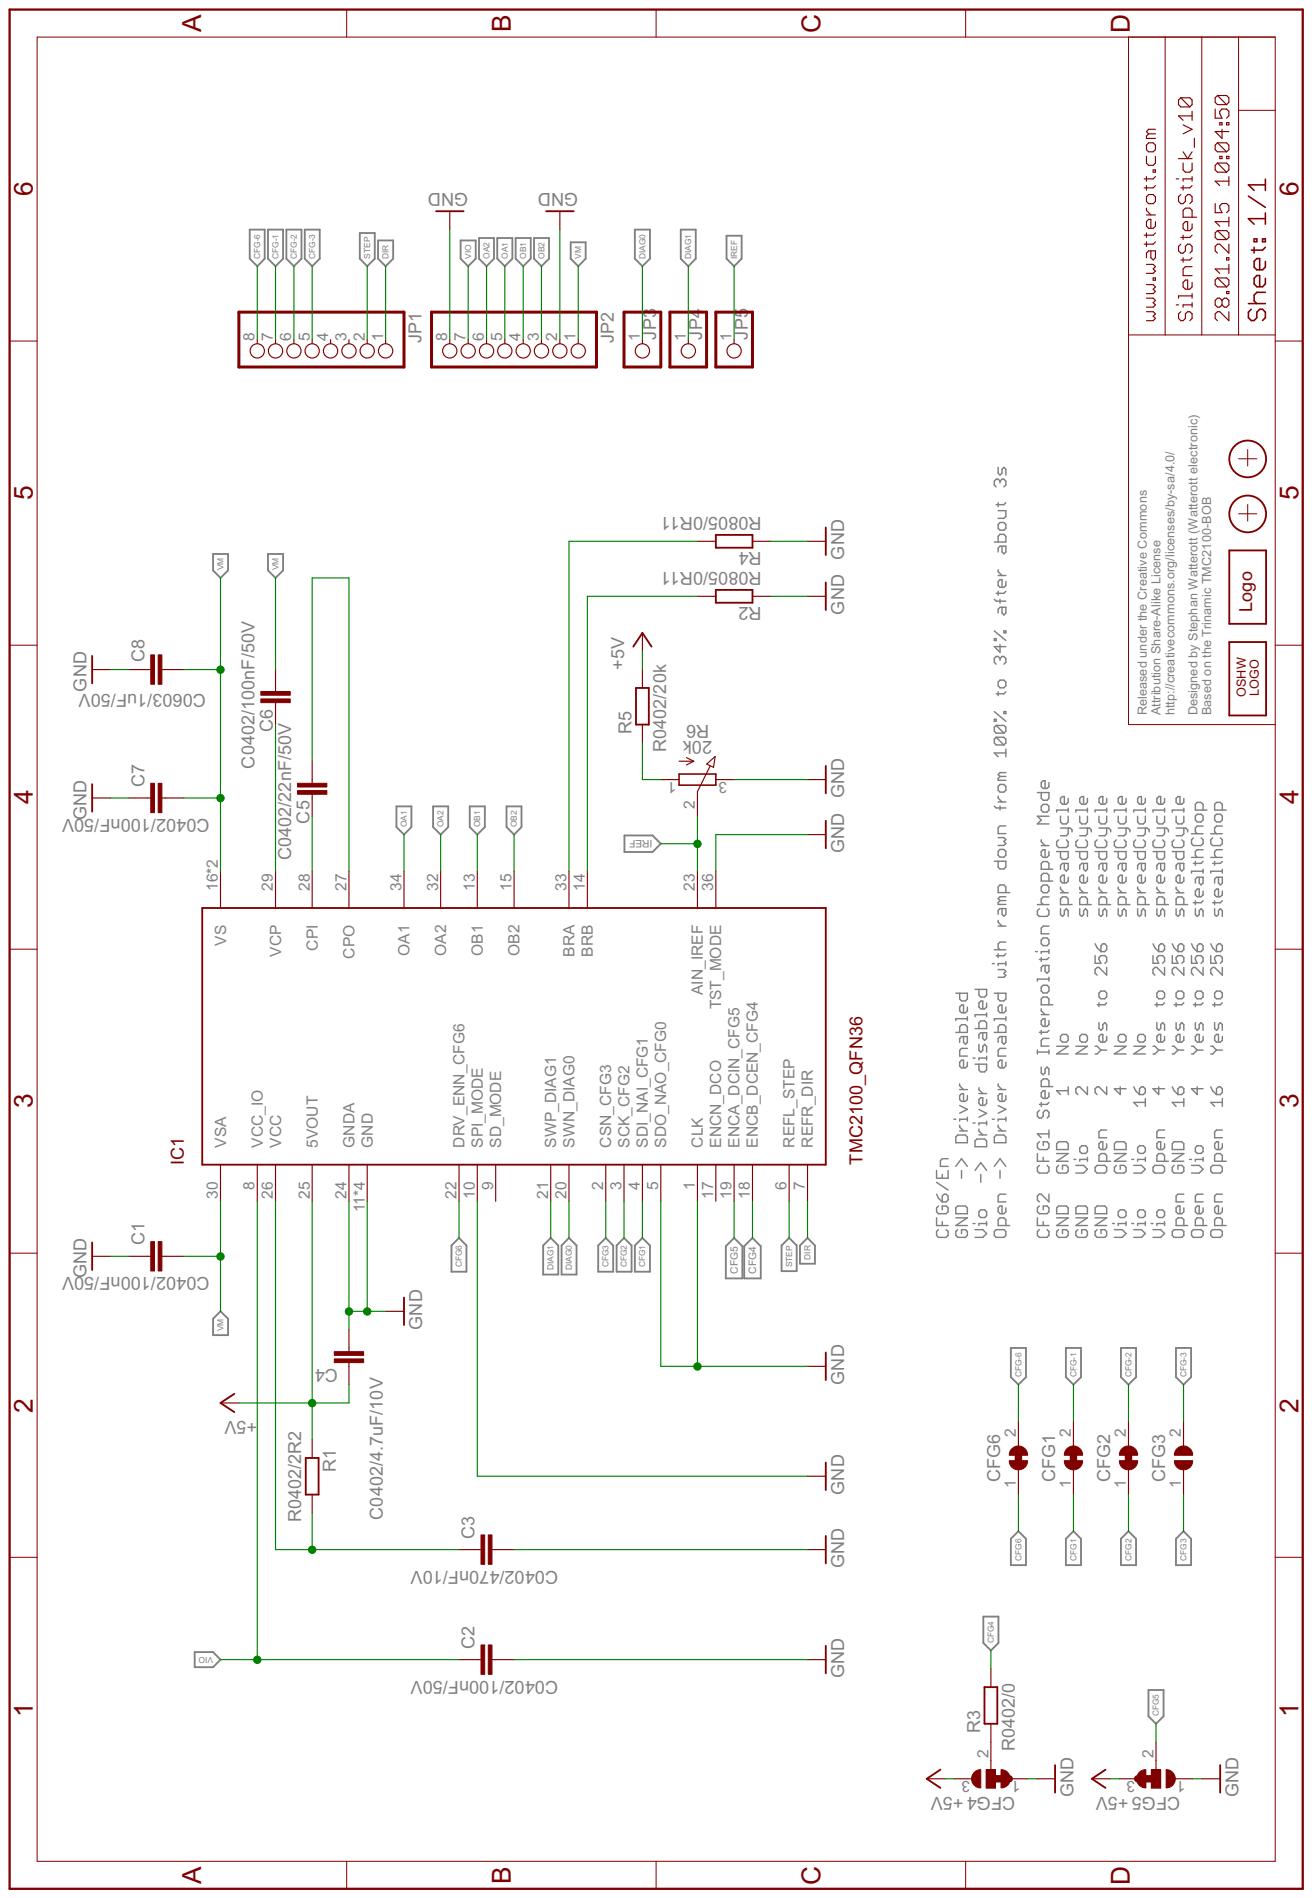
[picture p53: page 1]

http://creativecommons.org/licenses/by-sa/4.0/ Designed by Stephan Watterott (Watterott electronic) Based on the Trinamic TMC2100-BOB

Released under the Creative Commons Attribution Share-Alike License

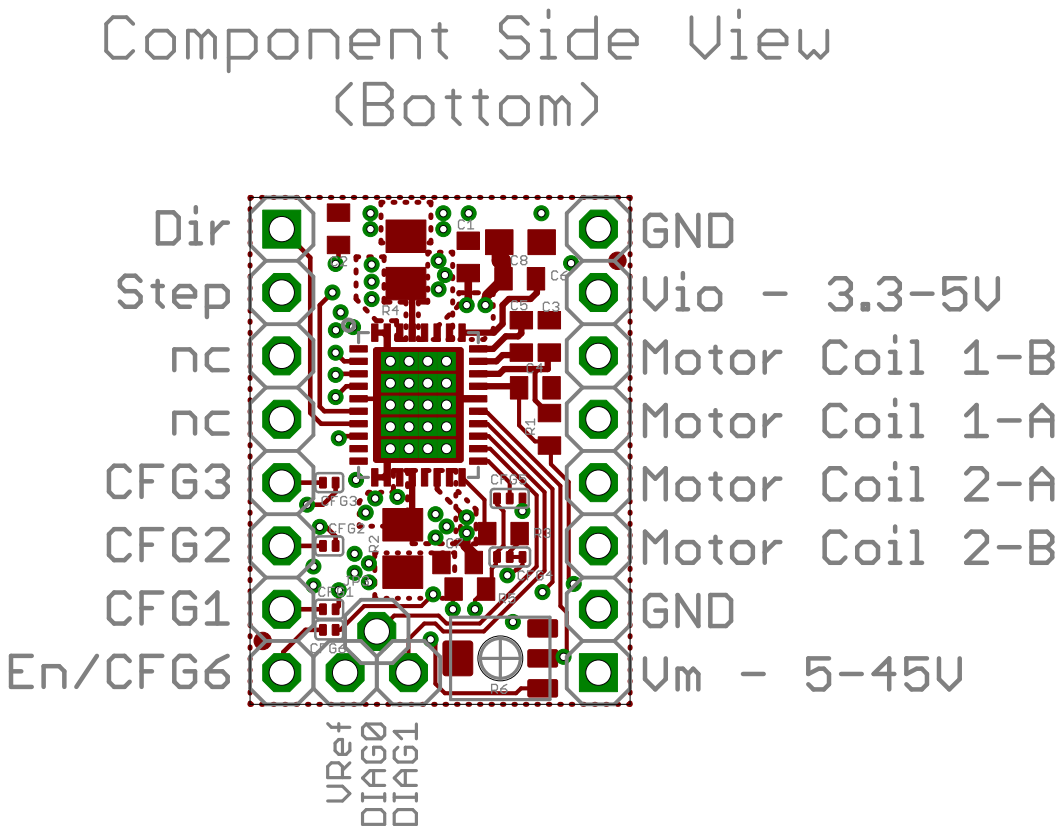
[picture p54: page 2]

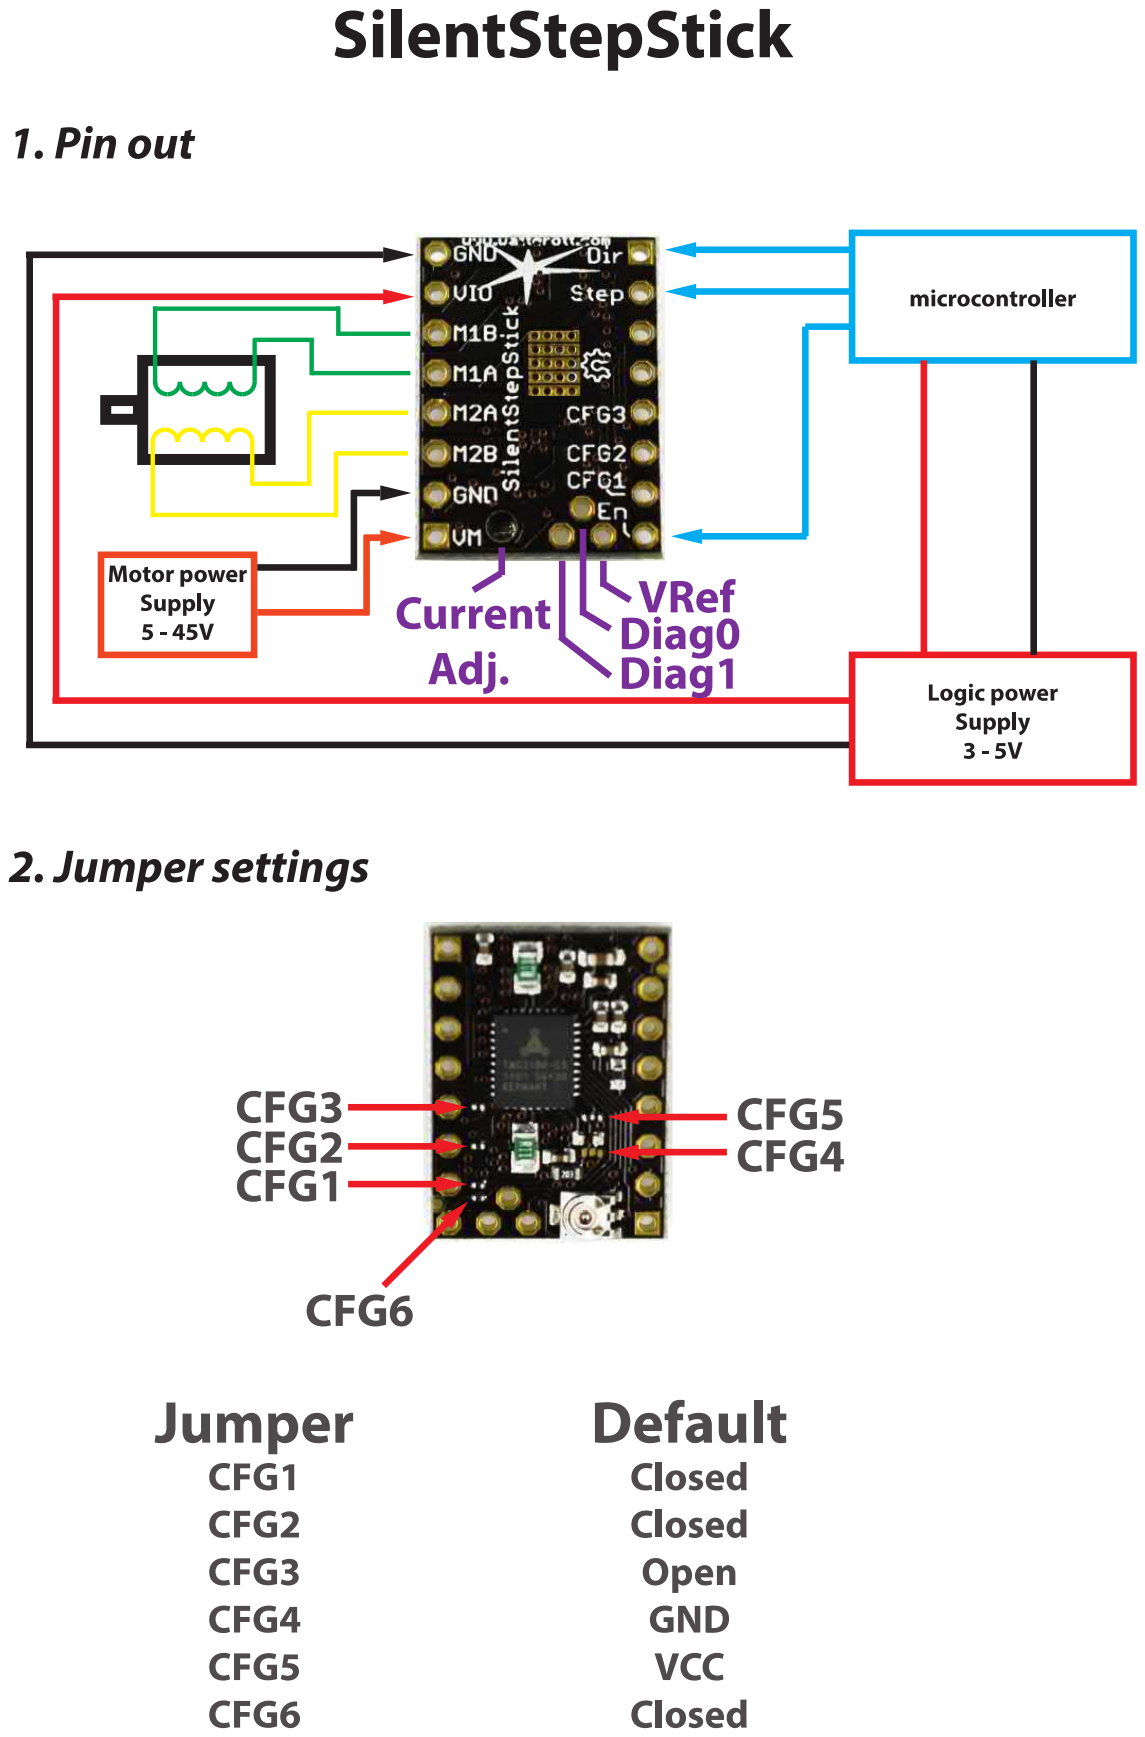
[picture p55: page 3]

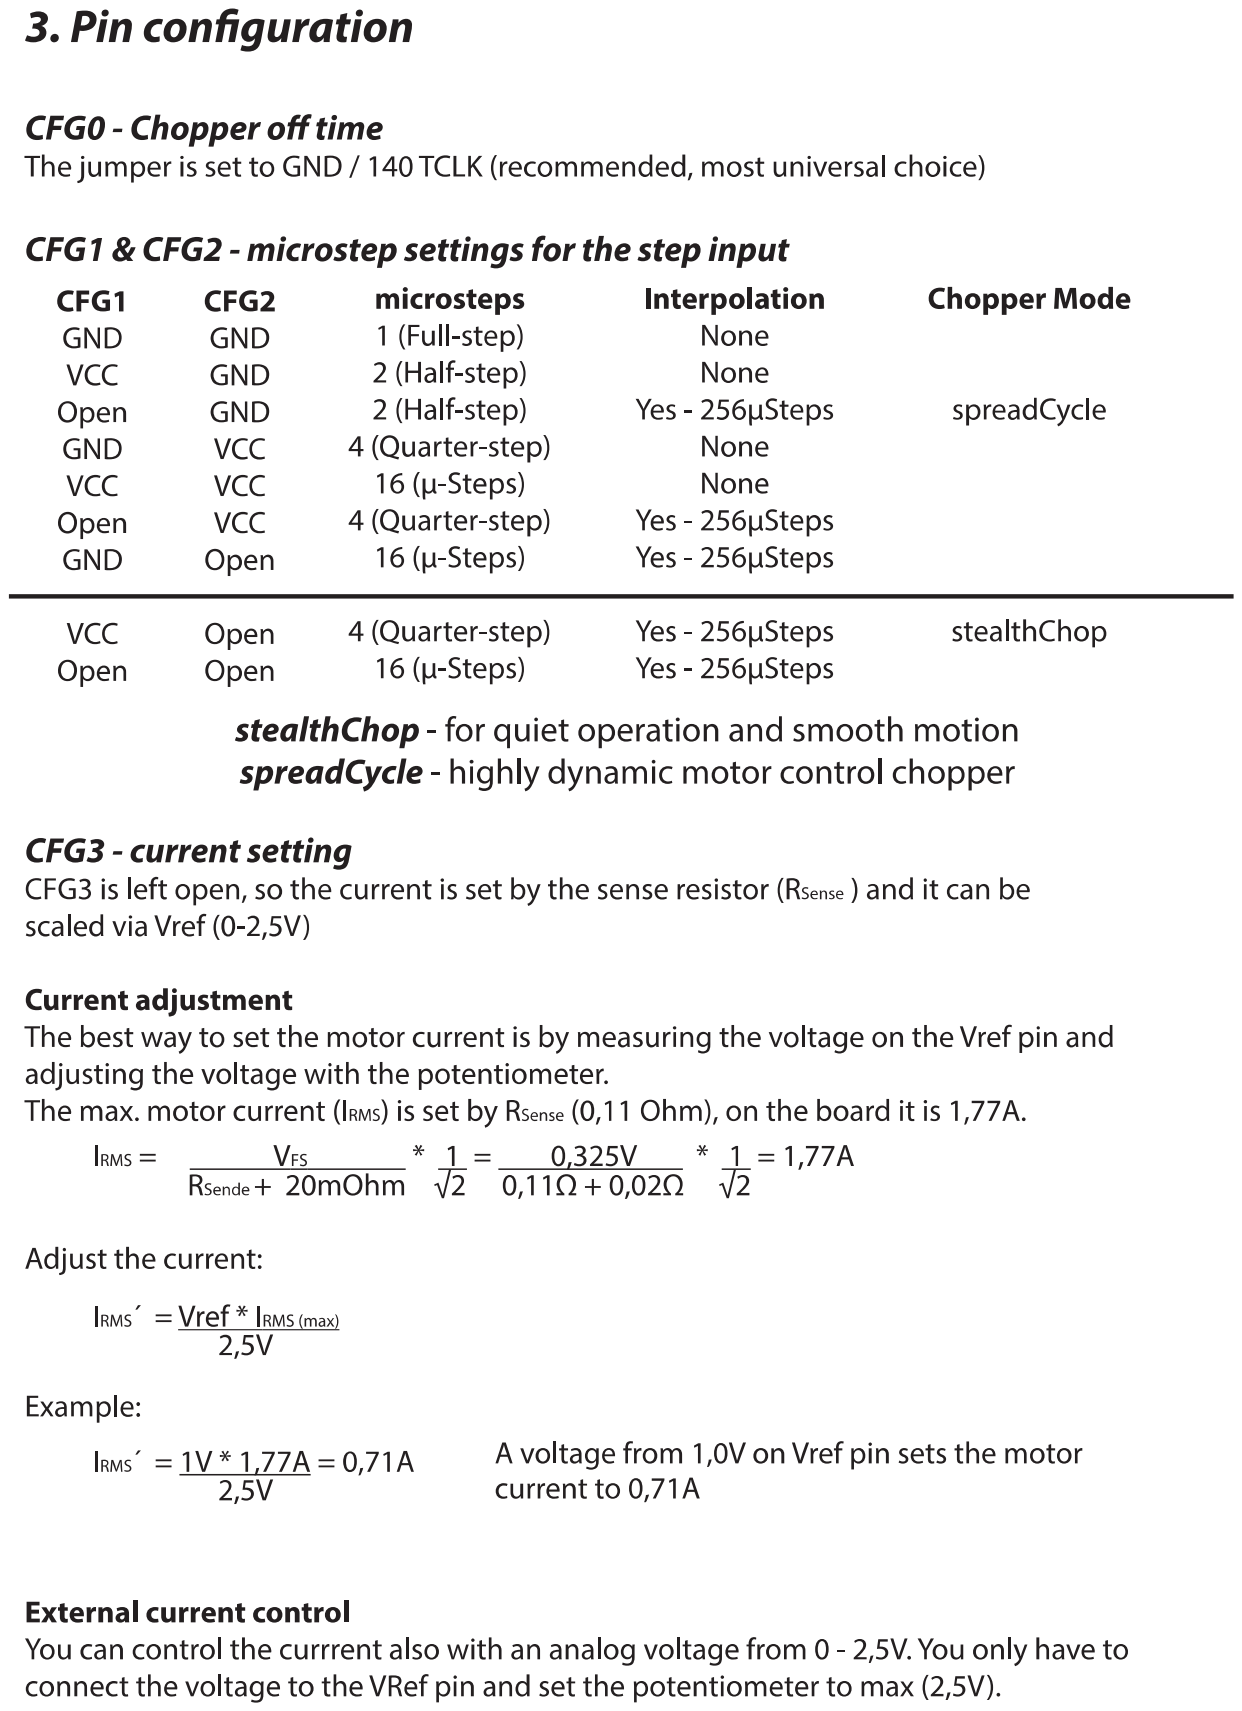
[picture p56: page 4]

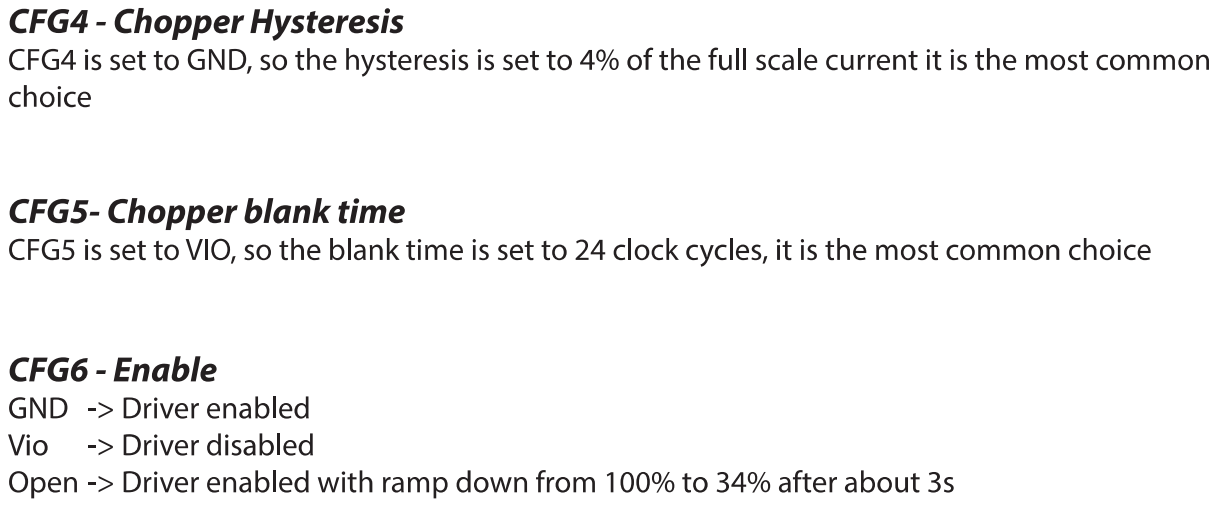
[picture p57: page 5]

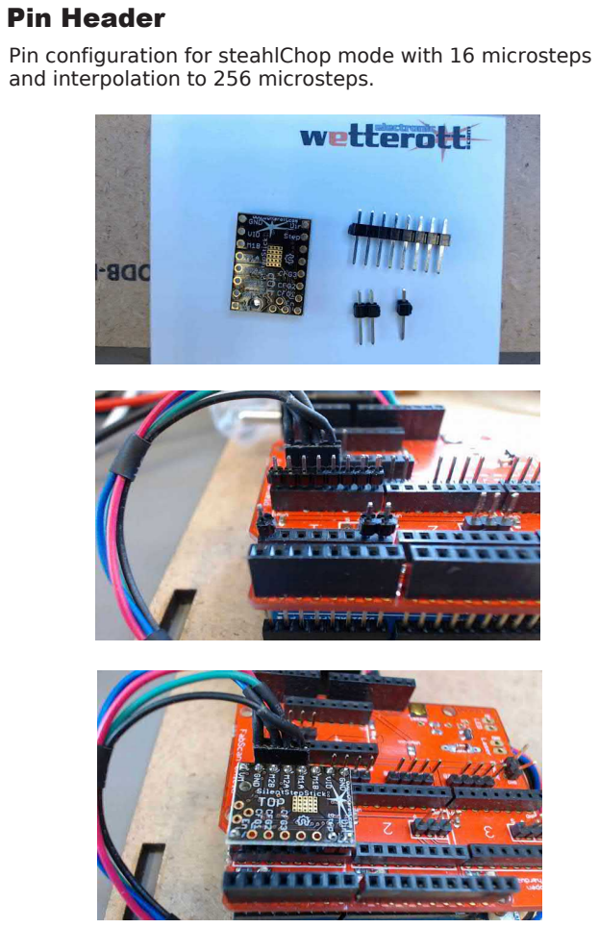
[picture p58: page 6]

Pin configuration for steahlChop mode with 16 microsteps
and interpolation to 256 microsteps.
