watterott/SilentStepStick/hardware/SilentStepStick-TMC2130_v11.brd

## EAGLE design hardware/SilentStepStick-TMC2130_v11.brd (2018-01-13, an earlier design)

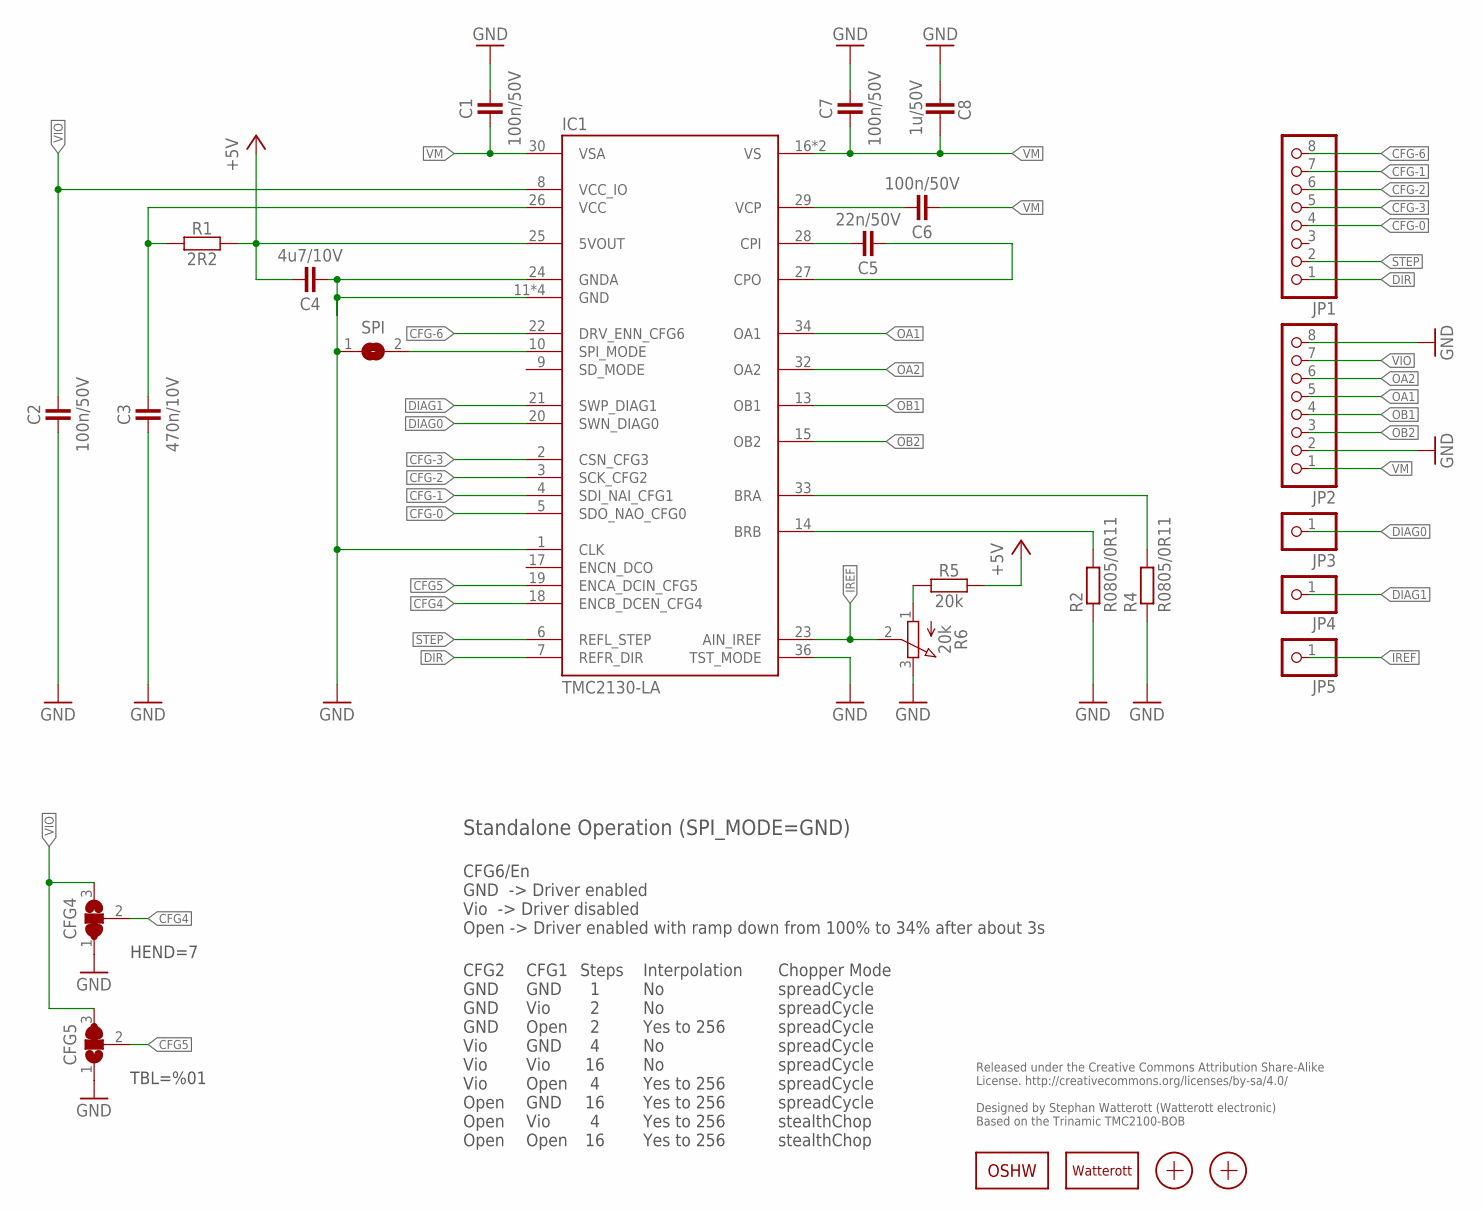
[picture p74: schematic SilentStepStick-TMC2130_v11.sch]

Parts:
C1, C2, C6, C7: 100n/50V; C0402
C3: 470n/10V; C0402
C4: 4u7/10V; C0402
C5: 22n/50V; C0402
C8: 1u/50V; C0603
CFG4, CFG5: JUMPER3-0201
IC1: TMC2130-LA; QFN36-PAD
JP1, JP2: PINHD-1X08_2.54-S; 1X08-S
JP3, JP4, JP5: PINHD-1X1; 1X01
LOGO1: OSHW_LOGOX0070; OSHW_6X70
LOGO2: LOGO-S_PLACE_M; SPARK_TPLACE_M
R1: 2R2; C0402
R2, R4: R0805/0R11; M0805
R5: 20k; C0402
R6: 20k; POT_EVM3R
SPI: JUMPER2-0402-NC; JUMPER2-0402_NC
X1, X2: PASSER-07; PASSER_07MM

Connections:
+5V: C4.2, IC1.25 (5VOUT), R1.2, R5.2
BRA: IC1.33 (BRA), R4.2
BRB: IC1.14 (BRB), R2.2
CFG4: CFG4.2, IC1.18 (ENCB_DCEN_CFG4)
CFG5: CFG5.2, IC1.19 (ENCA_DCIN_CFG5)
CFG-0: IC1.5 (SDO_NAO_CFG0), JP1.4
CFG-1: IC1.4 (SDI_NAI_CFG1), JP1.7
CFG-2: IC1.3 (SCK_CFG2), JP1.6
CFG-3: IC1.2 (CSN_CFG3), JP1.5
CFG-6: IC1.22 (DRV_ENN_CFG6), JP1.8
CPI: C5.2, IC1.28 (CPI)
CPO: C5.1, IC1.27 (CPO)
DIAG0: IC1.20 (SWN_DIAG0), JP3.1
DIAG1: IC1.21 (SWP_DIAG1), JP4.1
DIR: IC1.7 (REFR_DIR), JP1.1
GND: C1.2, C2.1, C3.1, C4.1, C7.2, C8.2, CFG4.1, CFG5.1, IC1.1 (CLK), IC1.11 (GND), IC1.12 (GND), IC1.24 (GNDA), IC1.35 (GND), IC1.36 (TST_MODE), IC1.TP (GND), JP2.2, JP2.8, R2.1, R4.1, R6.3 (E), SPI.1
IREF: IC1.23 (AIN_IREF), JP5.1, R6.2 (S)
unnamed: IC1.10 (SPI_MODE), SPI.2
OA1: IC1.34 (OA1), JP2.5
OA2: IC1.32 (OA2), JP2.6
OB1: IC1.13 (OB1), JP2.4
OB2: IC1.15 (OB2), JP2.3
STEP: IC1.6 (REFL_STEP), JP1.2
VCC: C3.2, IC1.26 (VCC), R1.1
VCP: C6.2, IC1.29 (VCP)
VIO: C2.2, CFG4.3, CFG5.3, IC1.8 (VCC_IO), JP2.7
VM: C1.1, C6.1, C7.1, C8.1, IC1.16 (VS), IC1.30 (VSA), IC1.31 (VS), JP2.1
VREF1: R5.1, R6.1 (A)

Notes on the sheet:
Released under the Creative Commons Attribution Share-Alike License. http://creativecommons.org/licenses/by-sa/4.0/ Designed by Stephan Watterott (Watterott electronic) Based on the Trinamic TMC2100-BOB
CFG6/En GND -> Driver enabled Vio -> Driver disabled Open -> Driver enabled with ramp down from 100% to 34% after about 3s
CFG2 GND GND GND Vio Vio Vio Open Open Open
CFG1 GND Vio Open GND Vio Open GND Vio Open
Steps 1 2 2 4 16 4 16 4 16
Interpolation No No Yes to 256 No No Yes to 256 Yes to 256 Yes to 256 Yes to 256
Chopper Mode spreadCycle spreadCycle spreadCycle spreadCycle spreadCycle spreadCycle spreadCycle stealthChop stealthChop
Standalone Operation (SPI_MODE=GND)
HEND=7
TBL=%01

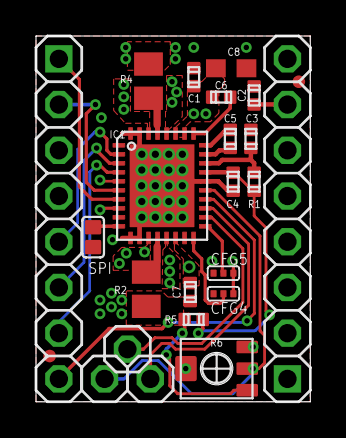
[picture p75: board SilentStepStick-TMC2130_v11.brd from above]

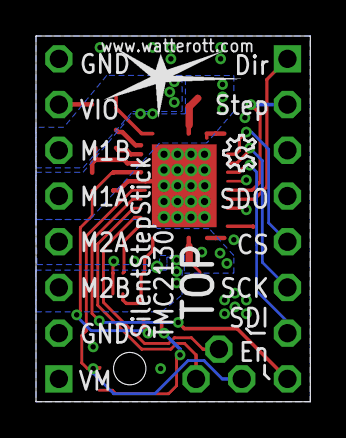
[picture p76: board SilentStepStick-TMC2130_v11.brd from below]

Board: 4 copper layers, 15.2 x 20.3 mm, 26 parts (2 on the bottom side), 28 nets.
