watterott/SilentStepStick/hardware/StepStick-Tester_v10.brd

## EAGLE design hardware/StepStick-Tester_v10.brd (2017-03-01)

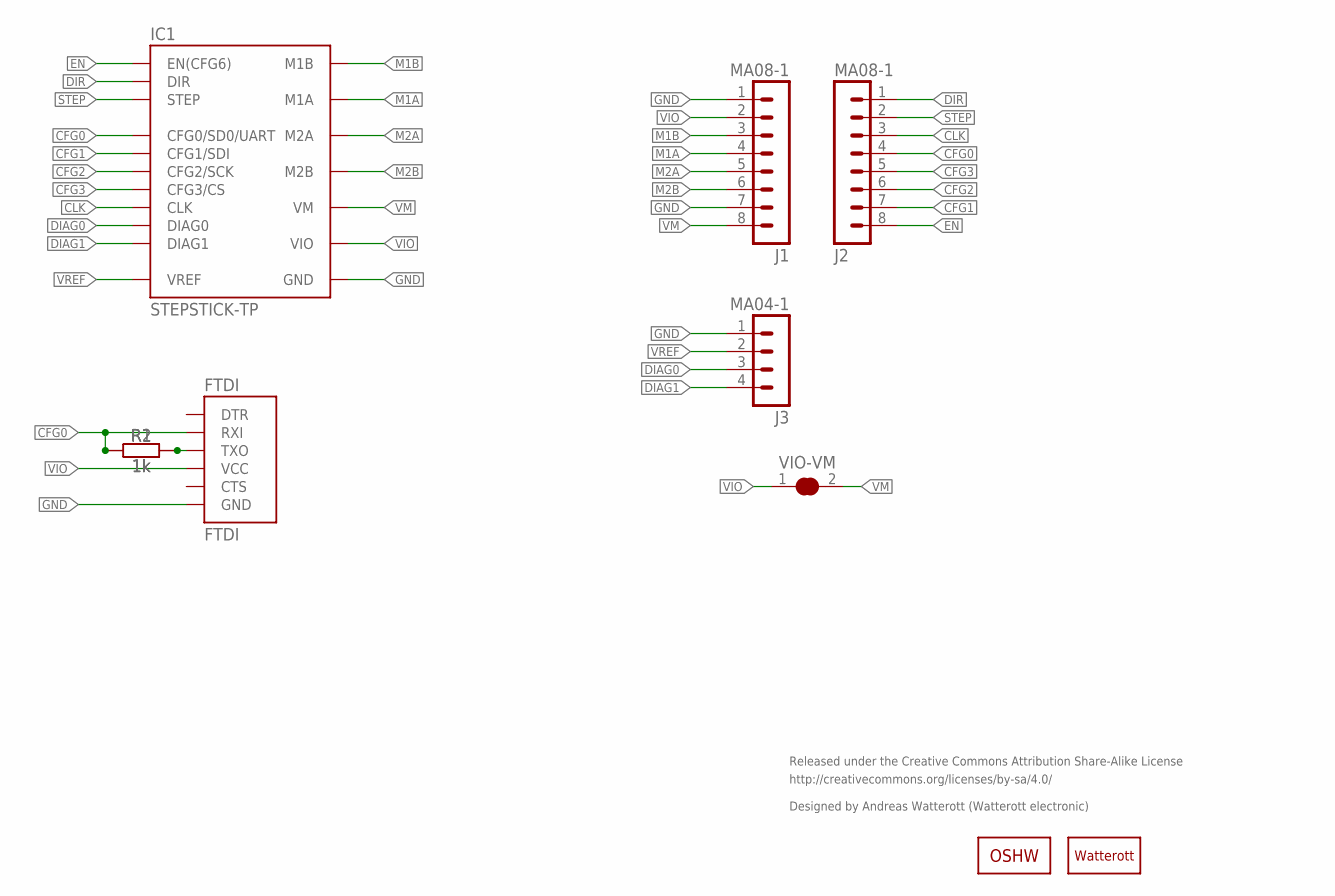
[picture p77: schematic StepStick-Tester_v10.sch]

Parts:
FTDI: FTDI
IC1: STEPSTICK-TP; STEPSTICK_TP
J1, J2: MA08-1
J3: MA04-1
LOGO1: OSHW_LOGOX0070; OSHW_6X70
LOGO2: LOGO-S_PLACE_S; SPARK_TPLACE_S
R1: 1k; R0207/7
R2: 1k; C0805
VIO-VM: JUMPER2-0603-NC; JUMPER2-0603_NC

Connections:
CFG0: FTDI.5-RXI (RXI), IC1.NC/CFG0 (CFG0/SD0/UART), J2.4, R1.1, R2.1
CFG1: IC1.CFG1 (CFG1/SDI), J2.7
CFG2: IC1.CFG2 (CFG2/SCK), J2.6
CFG3: IC1.CFG3 (CFG3/CS), J2.5
CLK: IC1.NC/CLK (CLK), J2.3
DIAG0: IC1.DIAG0, J3.3
DIAG1: IC1.DIAG1, J3.4
DIR: IC1.DIR, J2.1
EN: IC1.EN (EN(CFG6)), J2.8
GND: FTDI.1-GND (GND), IC1.GND@1 (GND), IC1.GND@2 (GND), J1.1, J1.7, J3.1
M1A: IC1.M1A, J1.4
M1B: IC1.M1B, J1.3
M2A: IC1.M2A, J1.5
M2B: IC1.M2B, J1.6
STEP: IC1.STEP, J2.2
TX: FTDI.4-TXO (TXO), R1.2, R2.2
VIO: FTDI.3-VCC (VCC), IC1.VIO, J1.2, VIO-VM.1
VM: IC1.VM, J1.8, VIO-VM.2
VREF: IC1.VREF, J3.2

Notes on the sheet:
Released under the Creative Commons Attribution Share-Alike License
http://creativecommons.org/licenses/by-sa/4.0/
Designed by Andreas Watterott (Watterott electronic)
