watterott/SilentStepStick/hardware/StepStick-Tester_v10.brd

## EAGLE design hardware/StepStick-Tester_v10.brd (continued)

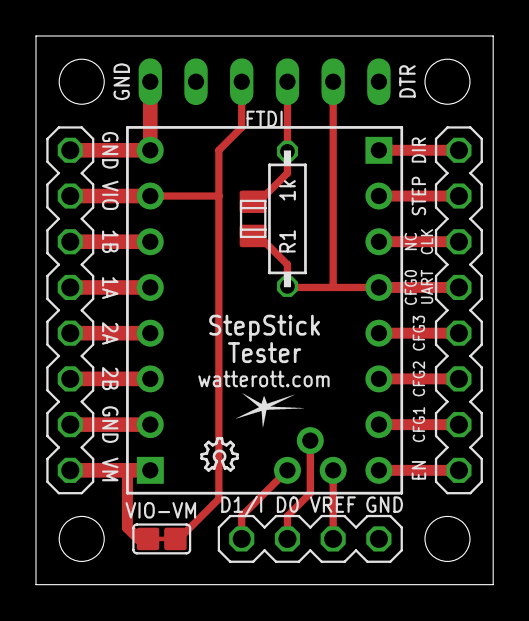
[picture p78: board StepStick-Tester_v10.brd from above]

Board: 2 copper layers, 25.4 x 30.5 mm, 10 parts (0 on the bottom side), 19 nets.
